savoirs-vivants/station-analyse-qualite-eau/firmware/Docs/latex/driver_f_r_a_m_8c.tex

\doxysection{C:\+/\+\+Users/\+valen/\+\+Documents/\+\+BUT GEII/\+\+SAE601/\+station\+\_\+analyse\+\_\+qualite\+\_\+eau/\+firmware/\+station\+\_\+analyse\+\_\+qualite\+\_\+eau/\+\+Core/\+\+Src/\+driver\+FRAM.c File Reference}
\hypertarget{driver_f_r_a_m_8c}{}\label{driver_f_r_a_m_8c}\index{C:/Users/valen/Documents/BUT GEII/SAE601/station\_analyse\_qualite\_eau/firmware/station\_analyse\_qualite\_eau/Core/Src/driverFRAM.c@{C:/Users/valen/Documents/BUT GEII/SAE601/station\_analyse\_qualite\_eau/firmware/station\_analyse\_qualite\_eau/Core/Src/driverFRAM.c}}
{\ttfamily \+\#include "{}driver\+FRAM.\+h"{}}\newline
{\ttfamily \+\#include $<$string.\+h$>$}\newline
Include dependency graph for driver\+FRAM.\+c:\+
\nopagebreak
\begin{figure}[H]
\begin{center}
\leavevmode
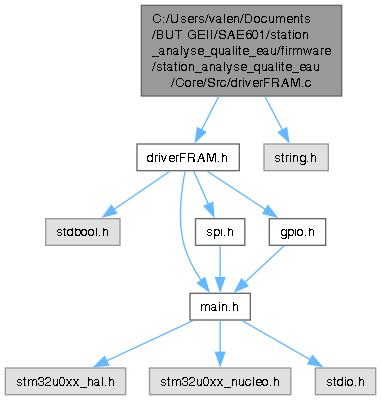
[picture p19: firmware/Docs/html/driver_f_r_a_m_8c__incl.png]

\end{center}
\end{figure}
\doxysubsubsection*{Functions}
\begin{DoxyCompactItemize}
\item 
\doxymbox{\hyperlink{driver_f_r_a_m_8h_a5c79796a1eed5fdbc3537a9758904619}{FRAM\+\_\+\+Result\+\_\+t}} \doxymbox{\hyperlink{driver_f_r_a_m_8c_a05c998c18403bda2555787fbaee7d2c4}{FRAM\+\_\+\+Init}} (\doxymbox{\hyperlink{struct_f_r_a_m__t}{FRAM\+\_\+t}} \texorpdfstring{$\ast$}{*}hfram, SPI\+\_\+\+Handle\+Type\+Def \texorpdfstring{$\ast$}{*}hspi, GPIO\+\_\+\+Type\+Def \texorpdfstring{$\ast$}{*}gpio\+\_\+port, uint16\+\_\+t gpio\+\_\+pin)
\begin{DoxyCompactList}\small\item\em Initialise la structure du driver et sécurise le bus SPI. \end{DoxyCompactList}\item 
\doxymbox{\hyperlink{driver_f_r_a_m_8h_a5c79796a1eed5fdbc3537a9758904619}{FRAM\+\_\+\+Result\+\_\+t}} \doxymbox{\hyperlink{driver_f_r_a_m_8c_a518d592a5f33b7c30320913e25c8d89a}{FRAM\+\_\+\+Write}} (\doxymbox{\hyperlink{struct_f_r_a_m__t}{FRAM\+\_\+t}} \texorpdfstring{$\ast$}{*}hfram, uint32\+\_\+t address, uint8\+\_\+t \texorpdfstring{$\ast$}{*}data, uint16\+\_\+t data\+\_\+size)
\begin{DoxyCompactList}\small\item\em Lance une opération asynchrone d\textquotesingle{}écriture vers la FRAM. \end{DoxyCompactList}\item 
\doxymbox{\hyperlink{driver_f_r_a_m_8h_a5c79796a1eed5fdbc3537a9758904619}{FRAM\+\_\+\+Result\+\_\+t}} \doxymbox{\hyperlink{driver_f_r_a_m_8c_a2ed88753d53d45f89881a459091a064d}{FRAM\+\_\+\+Read}} (\doxymbox{\hyperlink{struct_f_r_a_m__t}{FRAM\+\_\+t}} \texorpdfstring{$\ast$}{*}hfram, uint32\+\_\+t address, uint8\+\_\+t \texorpdfstring{$\ast$}{*}rx\+\_\+data, uint16\+\_\+t data\+\_\+size)
\begin{DoxyCompactList}\small\item\em Lance une opération asynchrone de lecture depuis la FRAM. \end{DoxyCompactList}\item 
\doxymbox{\hyperlink{driver_f_r_a_m_8h_aa90c9f46ed56211e7103e818904525b9}{FRAM\+\_\+\+Status\+\_\+t}} \doxymbox{\hyperlink{driver_f_r_a_m_8c_a352f682afba9d287e205c51423bc79ff}{FRAM\+\_\+\+Get\+Status}} (\doxymbox{\hyperlink{struct_f_r_a_m__t}{FRAM\+\_\+t}} \texorpdfstring{$\ast$}{*}hfram)
\begin{DoxyCompactList}\small\item\em Renvoie le statut opérationnel actuel du driver. \end{DoxyCompactList}\item 
void \doxymbox{\hyperlink{driver_f_r_a_m_8c_a218f6946717b10b3813b1979da4fce49}{FRAM\+\_\+\+Process}} (\doxymbox{\hyperlink{struct_f_r_a_m__t}{FRAM\+\_\+t}} \texorpdfstring{$\ast$}{*}hfram)
\begin{DoxyCompactList}\small\item\em Machine d\textquotesingle{}état du driver. Doit être appelée régulièrement dans la boucle principale. \end{DoxyCompactList}\item 
void \doxymbox{\hyperlink{driver_f_r_a_m_8c_aeafafd463d7b0a53c3f171c5a4949aa9}{FRAM\+\_\+\+Rx\+\_\+\+Callback}} (\doxymbox{\hyperlink{struct_f_r_a_m__t}{FRAM\+\_\+t}} \texorpdfstring{$\ast$}{*}hfram)
\begin{DoxyCompactList}\small\item\em Callback à appeler dans HAL\+\_\+\+SPI\+\_\+\+Rx\+Cplt\+Callback ou HAL\+\_\+\+SPI\+\_\+\+Tx\+Rx\+Cplt\+Callback. \end{DoxyCompactList}\item 
void \doxymbox{\hyperlink{driver_f_r_a_m_8c_a2b2faab018840ee82dca1baa6a25b1d0}{FRAM\+\_\+\+Tx\+\_\+\+Callback}} (\doxymbox{\hyperlink{struct_f_r_a_m__t}{FRAM\+\_\+t}} \texorpdfstring{$\ast$}{*}hfram)
\begin{DoxyCompactList}\small\item\em Callback à appeler dans HAL\+\_\+\+SPI\+\_\+\+Tx\+Cplt\+Callback. \end{DoxyCompactList}\end{DoxyCompactItemize}

\label{driver_f_r_a_m_8c_doc-func-members}
\Hypertarget{driver_f_r_a_m_8c_doc-func-members}
\doxysubsection{Function Documentation}
\Hypertarget{driver_f_r_a_m_8c_a352f682afba9d287e205c51423bc79ff}\index{driverFRAM.c@{driverFRAM.c}!FRAM\_GetStatus@{FRAM\_GetStatus}}
\index{FRAM\_GetStatus@{FRAM\_GetStatus}!driverFRAM.c@{driverFRAM.c}}
\doxysubsubsection{\texorpdfstring{FRAM\_GetStatus()}{FRAM\_GetStatus()}}
{\footnotesize\ttfamily \label{driver_f_r_a_m_8c_a352f682afba9d287e205c51423bc79ff} 
\doxymbox{\hyperlink{driver_f_r_a_m_8h_aa90c9f46ed56211e7103e818904525b9}{FRAM\+\_\+\+Status\+\_\+t}} FRAM\+\_\+\+Get\+Status (\begin{DoxyParamCaption}\item[{\doxymbox{\hyperlink{struct_f_r_a_m__t}{FRAM\+\_\+t}} \texorpdfstring{$\ast$}{*}}]{hfram}{}\end{DoxyParamCaption})}

Renvoie le statut opérationnel actuel du driver. 

\begin{DoxyParams}{Parameters}
{\em hfram} & Pointeur vers l\textquotesingle{}instance du driver FRAM. \\
\hline
\end{DoxyParams}
\begin{DoxyReturn}{Returns}
FRAM\+\_\+\+STATUS\+\_\+\+READY, FRAM\+\_\+\+STATUS\+\_\+\+BUSY, ou FRAM\+\_\+\+STATUS\+\_\+\+ERROR. 
\end{DoxyReturn}
\Hypertarget{driver_f_r_a_m_8c_a05c998c18403bda2555787fbaee7d2c4}\index{driverFRAM.c@{driverFRAM.c}!FRAM\_Init@{FRAM\_Init}}
\index{FRAM\_Init@{FRAM\_Init}!driverFRAM.c@{driverFRAM.c}}
\doxysubsubsection{\texorpdfstring{FRAM\_Init()}{FRAM\_Init()}}
{\footnotesize\ttfamily \label{driver_f_r_a_m_8c_a05c998c18403bda2555787fbaee7d2c4} 
\doxymbox{\hyperlink{driver_f_r_a_m_8h_a5c79796a1eed5fdbc3537a9758904619}{FRAM\+\_\+\+Result\+\_\+t}} FRAM\+\_\+\+Init (\begin{DoxyParamCaption}\item[{\doxymbox{\hyperlink{struct_f_r_a_m__t}{FRAM\+\_\+t}} \texorpdfstring{$\ast$}{*}}]{hfram}{, }\item[{SPI\+\_\+\+Handle\+Type\+Def \texorpdfstring{$\ast$}{*}}]{hspi}{, }\item[{GPIO\+\_\+\+Type\+Def \texorpdfstring{$\ast$}{*}}]{gpio\+\_\+port}{, }\item[{uint16\+\_\+t}]{gpio\+\_\+pin}{}\end{DoxyParamCaption})}

Initialise la structure du driver et sécurise le bus SPI. 

\begin{DoxyParams}{Parameters}
{\em hfram} & Pointeur vers l\textquotesingle{}instance du driver FRAM. \\
\hline
{\em hspi} & Pointeur vers le handle SPI (ex:\+ \&hspi3). \\
\hline
{\em gpio\+\_\+port} & Port GPIO du Chip Select. \\
\hline
{\em gpio\+\_\+pin} & Broche GPIO du Chip Select. \\
\hline
\end{DoxyParams}

\begin{DoxyRetVals}{Return values}
{\em FRAM\+\_\+\+OK} & si succès, sinon un code d\textquotesingle{}erreur synchrone (FRAM\+\_\+\+ERR\+\_\+\+PARAM). \\
\hline
\end{DoxyRetVals}
Here is the caller graph for this function:\+
\nopagebreak
\begin{figure}[H]
\begin{center}
\leavevmode

\end{center}
\end{figure}
\Hypertarget{driver_f_r_a_m_8c_a218f6946717b10b3813b1979da4fce49}\index{driverFRAM.c@{driverFRAM.c}!FRAM\_Process@{FRAM\_Process}}
\index{FRAM\_Process@{FRAM\_Process}!driverFRAM.c@{driverFRAM.c}}
\doxysubsubsection{\texorpdfstring{FRAM\_Process()}{FRAM\_Process()}}
{\footnotesize\ttfamily \label{driver_f_r_a_m_8c_a218f6946717b10b3813b1979da4fce49} 
void FRAM\+\_\+\+Process (\begin{DoxyParamCaption}\item[{\doxymbox{\hyperlink{struct_f_r_a_m__t}{FRAM\+\_\+t}} \texorpdfstring{$\ast$}{*}}]{hfram}{}\end{DoxyParamCaption})}

Machine d\textquotesingle{}état du driver. Doit être appelée régulièrement dans la boucle principale. 

\begin{DoxyParams}{Parameters}
{\em hfram} & Pointeur vers l\textquotesingle{}instance du driver FRAM. \\
\hline
\end{DoxyParams}
Here is the caller graph for this function:\+
\nopagebreak
\begin{figure}[H]
\begin{center}
\leavevmode

\end{center}
\end{figure}
\Hypertarget{driver_f_r_a_m_8c_a2ed88753d53d45f89881a459091a064d}\index{driverFRAM.c@{driverFRAM.c}!FRAM\_Read@{FRAM\_Read}}
\index{FRAM\_Read@{FRAM\_Read}!driverFRAM.c@{driverFRAM.c}}
\doxysubsubsection{\texorpdfstring{FRAM\_Read()}{FRAM\_Read()}}
{\footnotesize\ttfamily \label{driver_f_r_a_m_8c_a2ed88753d53d45f89881a459091a064d} 
\doxymbox{\hyperlink{driver_f_r_a_m_8h_a5c79796a1eed5fdbc3537a9758904619}{FRAM\+\_\+\+Result\+\_\+t}} FRAM\+\_\+\+Read (\begin{DoxyParamCaption}\item[{\doxymbox{\hyperlink{struct_f_r_a_m__t}{FRAM\+\_\+t}} \texorpdfstring{$\ast$}{*}}]{hfram}{, }\item[{uint32\+\_\+t}]{address}{, }\item[{uint8\+\_\+t \texorpdfstring{$\ast$}{*}}]{rx\+\_\+data}{, }\item[{uint16\+\_\+t}]{data\+\_\+size}{}\end{DoxyParamCaption})}

Lance une opération asynchrone de lecture depuis la FRAM. 

\begin{DoxyParams}{Parameters}
{\em hfram} & Pointeur vers l\textquotesingle{}instance du driver FRAM. \\
\hline
{\em address} & Adresse de départ en mémoire (doit être \texorpdfstring{$<$}{<} FRAM\+\_\+\+MAX\+\_\+\+ADDRESS). \\
\hline
{\em rx\+\_\+data} & Pointeur vers le buffer où stocker les données lues. \\
\hline
{\em data\+\_\+size} & Nombre d\textquotesingle{}octets à lire. \\
\hline
\end{DoxyParams}

\begin{DoxyRetVals}{Return values}
{\em FRAM\+\_\+\+OK} & si l\textquotesingle{}opération est acceptée, sinon un code d\textquotesingle{}erreur (BUSY, PARAM). \\
\hline
\end{DoxyRetVals}
Here is the caller graph for this function:\+
\nopagebreak
\begin{figure}[H]
\begin{center}
\leavevmode

\end{center}
\end{figure}
\Hypertarget{driver_f_r_a_m_8c_aeafafd463d7b0a53c3f171c5a4949aa9}\index{driverFRAM.c@{driverFRAM.c}!FRAM\_Rx\_Callback@{FRAM\_Rx\_Callback}}
\index{FRAM\_Rx\_Callback@{FRAM\_Rx\_Callback}!driverFRAM.c@{driverFRAM.c}}
\doxysubsubsection{\texorpdfstring{FRAM\_Rx\_Callback()}{FRAM\_Rx\_Callback()}}
{\footnotesize\ttfamily \label{driver_f_r_a_m_8c_aeafafd463d7b0a53c3f171c5a4949aa9} 
void FRAM\+\_\+\+Rx\+\_\+\+Callback (\begin{DoxyParamCaption}\item[{\doxymbox{\hyperlink{struct_f_r_a_m__t}{FRAM\+\_\+t}} \texorpdfstring{$\ast$}{*}}]{hfram}{}\end{DoxyParamCaption})}

Callback à appeler dans HAL\+\_\+\+SPI\+\_\+\+Rx\+Cplt\+Callback ou HAL\+\_\+\+SPI\+\_\+\+Tx\+Rx\+Cplt\+Callback. 

\begin{DoxyParams}{Parameters}
{\em hfram} & Pointeur vers l\textquotesingle{}instance du driver FRAM. \\
\hline
\end{DoxyParams}
Here is the caller graph for this function:\+
\nopagebreak
\begin{figure}[H]
\begin{center}
\leavevmode

\end{center}
\end{figure}
\Hypertarget{driver_f_r_a_m_8c_a2b2faab018840ee82dca1baa6a25b1d0}\index{driverFRAM.c@{driverFRAM.c}!FRAM\_Tx\_Callback@{FRAM\_Tx\_Callback}}
\index{FRAM\_Tx\_Callback@{FRAM\_Tx\_Callback}!driverFRAM.c@{driverFRAM.c}}
\doxysubsubsection{\texorpdfstring{FRAM\_Tx\_Callback()}{FRAM\_Tx\_Callback()}}
{\footnotesize\ttfamily \label{driver_f_r_a_m_8c_a2b2faab018840ee82dca1baa6a25b1d0} 
void FRAM\+\_\+\+Tx\+\_\+\+Callback (\begin{DoxyParamCaption}\item[{\doxymbox{\hyperlink{struct_f_r_a_m__t}{FRAM\+\_\+t}} \texorpdfstring{$\ast$}{*}}]{hfram}{}\end{DoxyParamCaption})}

Callback à appeler dans HAL\+\_\+\+SPI\+\_\+\+Tx\+Cplt\+Callback. 

\begin{DoxyParams}{Parameters}
{\em hfram} & Pointeur vers l\textquotesingle{}instance du driver FRAM. \\
\hline
\end{DoxyParams}
Here is the caller graph for this function:\+
\nopagebreak
\begin{figure}[H]
\begin{center}
\leavevmode

\end{center}
\end{figure}
\Hypertarget{driver_f_r_a_m_8c_a518d592a5f33b7c30320913e25c8d89a}\index{driverFRAM.c@{driverFRAM.c}!FRAM\_Write@{FRAM\_Write}}
\index{FRAM\_Write@{FRAM\_Write}!driverFRAM.c@{driverFRAM.c}}
\doxysubsubsection{\texorpdfstring{FRAM\_Write()}{FRAM\_Write()}}
{\footnotesize\ttfamily \label{driver_f_r_a_m_8c_a518d592a5f33b7c30320913e25c8d89a} 
\doxymbox{\hyperlink{driver_f_r_a_m_8h_a5c79796a1eed5fdbc3537a9758904619}{FRAM\+\_\+\+Result\+\_\+t}} FRAM\+\_\+\+Write (\begin{DoxyParamCaption}\item[{\doxymbox{\hyperlink{struct_f_r_a_m__t}{FRAM\+\_\+t}} \texorpdfstring{$\ast$}{*}}]{hfram}{, }\item[{uint32\+\_\+t}]{address}{, }\item[{uint8\+\_\+t \texorpdfstring{$\ast$}{*}}]{data}{, }\item[{uint16\+\_\+t}]{data\+\_\+size}{}\end{DoxyParamCaption})}

Lance une opération asynchrone d\textquotesingle{}écriture vers la FRAM. 

\begin{DoxyParams}{Parameters}
{\em hfram} & Pointeur vers l\textquotesingle{}instance du driver FRAM. \\
\hline
{\em address} & Adresse de départ en mémoire (doit être \texorpdfstring{$<$}{<} FRAM\+\_\+\+MAX\+\_\+\+ADDRESS). \\
\hline
{\em data} & Pointeur vers les données à écrire. \\
\hline
{\em data\+\_\+size} & Nombre d\textquotesingle{}octets à écrire. \\
\hline
\end{DoxyParams}

\begin{DoxyRetVals}{Return values}
{\em FRAM\+\_\+\+OK} & si l\textquotesingle{}opération est acceptée, sinon un code d\textquotesingle{}erreur (BUSY, PARAM). \\
\hline
\end{DoxyRetVals}
Here is the caller graph for this function:\+
\nopagebreak
\begin{figure}[H]
\begin{center}
\leavevmode

\end{center}
\end{figure}
