savoirs-vivants/station-analyse-qualite-eau/firmware/Docs/latex/driver_lo_ra_app_8c.tex

\doxysection{C:\+/\+\+Users/\+valen/\+\+Documents/\+\+BUT GEII/\+\+SAE601/\+station\+\_\+analyse\+\_\+qualite\+\_\+eau/\+firmware/\+station\+\_\+analyse\+\_\+qualite\+\_\+eau/\+\+Core/\+\+Src/\+driver\+Lo\+Ra\+App.c File Reference}
\hypertarget{driver_lo_ra_app_8c}{}\label{driver_lo_ra_app_8c}\index{C:/Users/valen/Documents/BUT GEII/SAE601/station\_analyse\_qualite\_eau/firmware/station\_analyse\_qualite\_eau/Core/Src/driverLoRaApp.c@{C:/Users/valen/Documents/BUT GEII/SAE601/station\_analyse\_qualite\_eau/firmware/station\_analyse\_qualite\_eau/Core/Src/driverLoRaApp.c}}
{\ttfamily \+\#include "{}driver\+Lo\+Ra\+App.\+h"{}}\newline
Include dependency graph for driver\+Lo\+Ra\+App.\+c:\+
\nopagebreak
\begin{figure}[H]
\begin{center}
\leavevmode
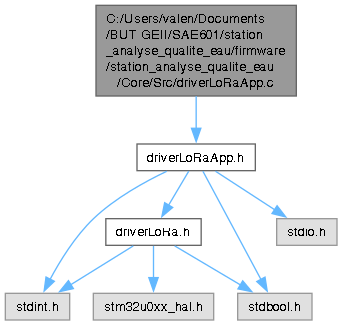
[picture p28: firmware/Docs/html/driver_lo_ra_app_8c__incl.png]

\end{center}
\end{figure}
\doxysubsubsection*{Functions}
\begin{DoxyCompactItemize}
\item 
void \doxymbox{\hyperlink{driver_lo_ra_app_8c_a42db2c6d3925f1c86ebfdd004cc7da83}{Lo\+Ra\+\_\+\+App\+\_\+\+Init}} (\doxymbox{\hyperlink{struct_lo_ra_w_a_n___manager__t}{Lo\+Ra\+WAN\+\_\+\+Manager\+\_\+t}} \texorpdfstring{$\ast$}{*}hlorapp, \doxymbox{\hyperlink{struct_lo_ra__t}{Lo\+Ra\+\_\+t}} \texorpdfstring{$\ast$}{*}hlora, const \doxymbox{\hyperlink{struct_lo_ra___command__t}{Lo\+Ra\+\_\+\+Command\+\_\+t}} \texorpdfstring{$\ast$}{*}cmds)
\item 
void \doxymbox{\hyperlink{driver_lo_ra_app_8c_a6f48cdb117beed1327cee06821cd0800}{Lo\+Ra\+\_\+\+App\+\_\+\+Process}} (\doxymbox{\hyperlink{struct_lo_ra_w_a_n___manager__t}{Lo\+Ra\+WAN\+\_\+\+Manager\+\_\+t}} \texorpdfstring{$\ast$}{*}hlorapp)
\end{DoxyCompactItemize}

\label{driver_lo_ra_app_8c_doc-func-members}
\Hypertarget{driver_lo_ra_app_8c_doc-func-members}
\doxysubsection{Function Documentation}
\Hypertarget{driver_lo_ra_app_8c_a42db2c6d3925f1c86ebfdd004cc7da83}\index{driverLoRaApp.c@{driverLoRaApp.c}!LoRa\_App\_Init@{LoRa\_App\_Init}}
\index{LoRa\_App\_Init@{LoRa\_App\_Init}!driverLoRaApp.c@{driverLoRaApp.c}}
\doxysubsubsection{\texorpdfstring{LoRa\_App\_Init()}{LoRa\_App\_Init()}}
{\footnotesize\ttfamily \label{driver_lo_ra_app_8c_a42db2c6d3925f1c86ebfdd004cc7da83} 
void Lo\+Ra\+\_\+\+App\+\_\+\+Init (\begin{DoxyParamCaption}\item[{\doxymbox{\hyperlink{struct_lo_ra_w_a_n___manager__t}{Lo\+Ra\+WAN\+\_\+\+Manager\+\_\+t}} \texorpdfstring{$\ast$}{*}}]{hlorapp}{, }\item[{\doxymbox{\hyperlink{struct_lo_ra__t}{Lo\+Ra\+\_\+t}} \texorpdfstring{$\ast$}{*}}]{hlora}{, }\item[{const \doxymbox{\hyperlink{struct_lo_ra___command__t}{Lo\+Ra\+\_\+\+Command\+\_\+t}} \texorpdfstring{$\ast$}{*}}]{cmds}{}\end{DoxyParamCaption})}

\Hypertarget{driver_lo_ra_app_8c_a6f48cdb117beed1327cee06821cd0800}\index{driverLoRaApp.c@{driverLoRaApp.c}!LoRa\_App\_Process@{LoRa\_App\_Process}}
\index{LoRa\_App\_Process@{LoRa\_App\_Process}!driverLoRaApp.c@{driverLoRaApp.c}}
\doxysubsubsection{\texorpdfstring{LoRa\_App\_Process()}{LoRa\_App\_Process()}}
{\footnotesize\ttfamily \label{driver_lo_ra_app_8c_a6f48cdb117beed1327cee06821cd0800} 
void Lo\+Ra\+\_\+\+App\+\_\+\+Process (\begin{DoxyParamCaption}\item[{\doxymbox{\hyperlink{struct_lo_ra_w_a_n___manager__t}{Lo\+Ra\+WAN\+\_\+\+Manager\+\_\+t}} \texorpdfstring{$\ast$}{*}}]{hlorapp}{}\end{DoxyParamCaption})}

Here is the call graph for this function:\+
\nopagebreak
\begin{figure}[H]
\begin{center}
\leavevmode

\end{center}
\end{figure}
