savoirs-vivants/station-analyse-qualite-eau/firmware/Docs/latex/driver_lo_ra_app_8h.tex

\doxysection{C:\+/\+\+Users/\+valen/\+\+Documents/\+\+BUT GEII/\+\+SAE601/\+station\+\_\+analyse\+\_\+qualite\+\_\+eau/\+firmware/\+station\+\_\+analyse\+\_\+qualite\+\_\+eau/\+\+Core/\+\+Inc/\+driver\+Lo\+Ra\+App.h File Reference}
\hypertarget{driver_lo_ra_app_8h}{}\label{driver_lo_ra_app_8h}\index{C:/Users/valen/Documents/BUT GEII/SAE601/station\_analyse\_qualite\_eau/firmware/station\_analyse\_qualite\_eau/Core/Inc/driverLoRaApp.h@{C:/Users/valen/Documents/BUT GEII/SAE601/station\_analyse\_qualite\_eau/firmware/station\_analyse\_qualite\_eau/Core/Inc/driverLoRaApp.h}}
{\ttfamily \+\#include $<$stdint.\+h$>$}\newline
{\ttfamily \+\#include $<$stdbool.\+h$>$}\newline
{\ttfamily \+\#include $<$stdio.\+h$>$}\newline
{\ttfamily \+\#include "{}driver\+Lo\+Ra.\+h"{}}\newline
Include dependency graph for driver\+Lo\+Ra\+App.\+h:\+
\nopagebreak
\begin{figure}[H]
\begin{center}
\leavevmode
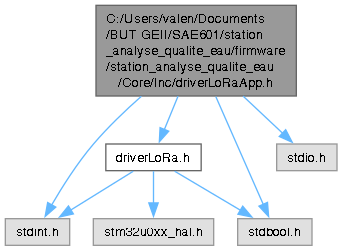
[picture p29: firmware/Docs/html/driver_lo_ra_app_8h__incl.png]

\end{center}
\end{figure}
This graph shows which files directly or indirectly include this file:\+
\nopagebreak
\begin{figure}[H]
\begin{center}
\leavevmode
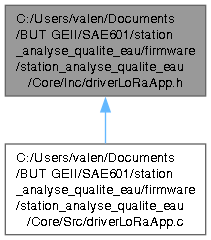
[picture p30: firmware/Docs/html/driver_lo_ra_app_8h__dep__incl.png]

\end{center}
\end{figure}
\doxysubsubsection*{Data Structures}
\begin{DoxyCompactItemize}
\item 
struct \doxymbox{\hyperlink{struct_lo_ra___command__t}{Lo\+Ra\+\_\+\+Command\+\_\+t}}
\item 
struct \doxymbox{\hyperlink{struct_lo_ra_w_a_n___manager__t}{Lo\+Ra\+WAN\+\_\+\+Manager\+\_\+t}}
\end{DoxyCompactItemize}
\doxysubsubsection*{Functions}
\begin{DoxyCompactItemize}
\item 
void \doxymbox{\hyperlink{driver_lo_ra_app_8h_a42db2c6d3925f1c86ebfdd004cc7da83}{Lo\+Ra\+\_\+\+App\+\_\+\+Init}} (\doxymbox{\hyperlink{struct_lo_ra_w_a_n___manager__t}{Lo\+Ra\+WAN\+\_\+\+Manager\+\_\+t}} \texorpdfstring{$\ast$}{*}hlorapp, \doxymbox{\hyperlink{struct_lo_ra__t}{Lo\+Ra\+\_\+t}} \texorpdfstring{$\ast$}{*}hlora, const \doxymbox{\hyperlink{struct_lo_ra___command__t}{Lo\+Ra\+\_\+\+Command\+\_\+t}} \texorpdfstring{$\ast$}{*}cmds)
\item 
void \doxymbox{\hyperlink{driver_lo_ra_app_8h_a6f48cdb117beed1327cee06821cd0800}{Lo\+Ra\+\_\+\+App\+\_\+\+Process}} (\doxymbox{\hyperlink{struct_lo_ra_w_a_n___manager__t}{Lo\+Ra\+WAN\+\_\+\+Manager\+\_\+t}} \texorpdfstring{$\ast$}{*}hlorapp)
\end{DoxyCompactItemize}

\label{driver_lo_ra_app_8h_doc-func-members}
\Hypertarget{driver_lo_ra_app_8h_doc-func-members}
\doxysubsection{Function Documentation}
\Hypertarget{driver_lo_ra_app_8h_a42db2c6d3925f1c86ebfdd004cc7da83}\index{driverLoRaApp.h@{driverLoRaApp.h}!LoRa\_App\_Init@{LoRa\_App\_Init}}
\index{LoRa\_App\_Init@{LoRa\_App\_Init}!driverLoRaApp.h@{driverLoRaApp.h}}
\doxysubsubsection{\texorpdfstring{LoRa\_App\_Init()}{LoRa\_App\_Init()}}
{\footnotesize\ttfamily \label{driver_lo_ra_app_8h_a42db2c6d3925f1c86ebfdd004cc7da83} 
void Lo\+Ra\+\_\+\+App\+\_\+\+Init (\begin{DoxyParamCaption}\item[{\doxymbox{\hyperlink{struct_lo_ra_w_a_n___manager__t}{Lo\+Ra\+WAN\+\_\+\+Manager\+\_\+t}} \texorpdfstring{$\ast$}{*}}]{hlorapp}{, }\item[{\doxymbox{\hyperlink{struct_lo_ra__t}{Lo\+Ra\+\_\+t}} \texorpdfstring{$\ast$}{*}}]{hlora}{, }\item[{const \doxymbox{\hyperlink{struct_lo_ra___command__t}{Lo\+Ra\+\_\+\+Command\+\_\+t}} \texorpdfstring{$\ast$}{*}}]{cmds}{}\end{DoxyParamCaption})}

\Hypertarget{driver_lo_ra_app_8h_a6f48cdb117beed1327cee06821cd0800}\index{driverLoRaApp.h@{driverLoRaApp.h}!LoRa\_App\_Process@{LoRa\_App\_Process}}
\index{LoRa\_App\_Process@{LoRa\_App\_Process}!driverLoRaApp.h@{driverLoRaApp.h}}
\doxysubsubsection{\texorpdfstring{LoRa\_App\_Process()}{LoRa\_App\_Process()}}
{\footnotesize\ttfamily \label{driver_lo_ra_app_8h_a6f48cdb117beed1327cee06821cd0800} 
void Lo\+Ra\+\_\+\+App\+\_\+\+Process (\begin{DoxyParamCaption}\item[{\doxymbox{\hyperlink{struct_lo_ra_w_a_n___manager__t}{Lo\+Ra\+WAN\+\_\+\+Manager\+\_\+t}} \texorpdfstring{$\ast$}{*}}]{hlorapp}{}\end{DoxyParamCaption})}

Here is the call graph for this function:\+
\nopagebreak
\begin{figure}[H]
\begin{center}
\leavevmode

\end{center}
\end{figure}
