savoirs-vivants/station-analyse-qualite-eau/firmware/Docs/latex/driver_r_t_c_8c.tex

\doxysection{C:\+/\+\+Users/\+valen/\+\+Documents/\+\+BUT GEII/\+\+SAE601/\+station\+\_\+analyse\+\_\+qualite\+\_\+eau/\+firmware/\+station\+\_\+analyse\+\_\+qualite\+\_\+eau/\+\+Core/\+\+Src/\+driver\+RTC.c File Reference}
\hypertarget{driver_r_t_c_8c}{}\label{driver_r_t_c_8c}\index{C:/Users/valen/Documents/BUT GEII/SAE601/station\_analyse\_qualite\_eau/firmware/station\_analyse\_qualite\_eau/Core/Src/driverRTC.c@{C:/Users/valen/Documents/BUT GEII/SAE601/station\_analyse\_qualite\_eau/firmware/station\_analyse\_qualite\_eau/Core/Src/driverRTC.c}}
{\ttfamily \+\#include "{}driver\+RTC.\+h"{}}\newline
Include dependency graph for driver\+RTC.\+c:\+
\nopagebreak
\begin{figure}[H]
\begin{center}
\leavevmode
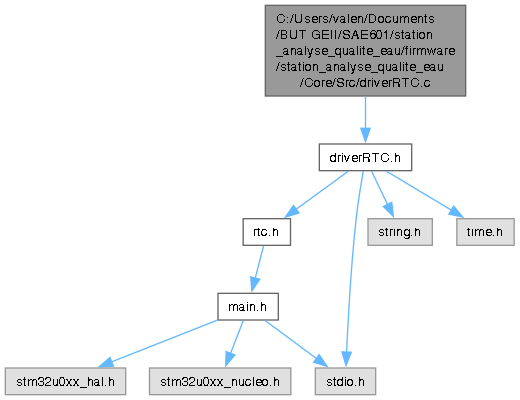
[picture p34: firmware/Docs/html/driver_r_t_c_8c__incl.png]

\end{center}
\end{figure}
\doxysubsubsection*{Functions}
\begin{DoxyCompactItemize}
\item 
void \doxymbox{\hyperlink{driver_r_t_c_8c_a494a13f6dc06fc1b330d8ac7f15f1c67}{config\+RTC}} (RTC\+\_\+\+Handle\+Type\+Def \texorpdfstring{$\ast$}{*}hrtc, RTC\+\_\+\+Time\+Type\+Def \texorpdfstring{$\ast$}{*}s\+Time, RTC\+\_\+\+Date\+Type\+Def \texorpdfstring{$\ast$}{*}s\+Date)
\item 
uint32\+\_\+t \doxymbox{\hyperlink{driver_r_t_c_8c_adaa0993b12bc61940e096e6a8d791dcd}{Get\+\_\+\+UNIX\+\_\+\+Timestamp}} (RTC\+\_\+\+Time\+Type\+Def \texorpdfstring{$\ast$}{*}s\+Time\+\_\+read, RTC\+\_\+\+Date\+Type\+Def \texorpdfstring{$\ast$}{*}s\+Date\+\_\+read)
\end{DoxyCompactItemize}

\label{driver_r_t_c_8c_doc-func-members}
\Hypertarget{driver_r_t_c_8c_doc-func-members}
\doxysubsection{Function Documentation}
\Hypertarget{driver_r_t_c_8c_a494a13f6dc06fc1b330d8ac7f15f1c67}\index{driverRTC.c@{driverRTC.c}!configRTC@{configRTC}}
\index{configRTC@{configRTC}!driverRTC.c@{driverRTC.c}}
\doxysubsubsection{\texorpdfstring{configRTC()}{configRTC()}}
{\footnotesize\ttfamily \label{driver_r_t_c_8c_a494a13f6dc06fc1b330d8ac7f15f1c67} 
void config\+RTC (\begin{DoxyParamCaption}\item[{RTC\+\_\+\+Handle\+Type\+Def \texorpdfstring{$\ast$}{*}}]{hrtc}{, }\item[{RTC\+\_\+\+Time\+Type\+Def \texorpdfstring{$\ast$}{*}}]{s\+Time}{, }\item[{RTC\+\_\+\+Date\+Type\+Def \texorpdfstring{$\ast$}{*}}]{s\+Date}{}\end{DoxyParamCaption})}

Here is the call graph for this function:\+
\nopagebreak
\begin{figure}[H]
\begin{center}
\leavevmode

\end{center}
\end{figure}
Here is the caller graph for this function:\+
\nopagebreak
\begin{figure}[H]
\begin{center}
\leavevmode

\end{center}
\end{figure}
\Hypertarget{driver_r_t_c_8c_adaa0993b12bc61940e096e6a8d791dcd}\index{driverRTC.c@{driverRTC.c}!Get\_UNIX\_Timestamp@{Get\_UNIX\_Timestamp}}
\index{Get\_UNIX\_Timestamp@{Get\_UNIX\_Timestamp}!driverRTC.c@{driverRTC.c}}
\doxysubsubsection{\texorpdfstring{Get\_UNIX\_Timestamp()}{Get\_UNIX\_Timestamp()}}
{\footnotesize\ttfamily \label{driver_r_t_c_8c_adaa0993b12bc61940e096e6a8d791dcd} 
uint32\+\_\+t Get\+\_\+\+UNIX\+\_\+\+Timestamp (\begin{DoxyParamCaption}\item[{RTC\+\_\+\+Time\+Type\+Def \texorpdfstring{$\ast$}{*}}]{s\+Time\+\_\+read}{, }\item[{RTC\+\_\+\+Date\+Type\+Def \texorpdfstring{$\ast$}{*}}]{s\+Date\+\_\+read}{}\end{DoxyParamCaption})}

Here is the caller graph for this function:\+
\nopagebreak
\begin{figure}[H]
\begin{center}
\leavevmode

\end{center}
\end{figure}
