savoirs-vivants/station-analyse-qualite-eau/firmware/Docs/latex/driver_r_t_c_8h.tex

\doxysection{C:\+/\+\+Users/\+valen/\+\+Documents/\+\+BUT GEII/\+\+SAE601/\+station\+\_\+analyse\+\_\+qualite\+\_\+eau/\+firmware/\+station\+\_\+analyse\+\_\+qualite\+\_\+eau/\+\+Core/\+\+Inc/\+driver\+RTC.h File Reference}
\hypertarget{driver_r_t_c_8h}{}\label{driver_r_t_c_8h}\index{C:/Users/valen/Documents/BUT GEII/SAE601/station\_analyse\_qualite\_eau/firmware/station\_analyse\_qualite\_eau/Core/Inc/driverRTC.h@{C:/Users/valen/Documents/BUT GEII/SAE601/station\_analyse\_qualite\_eau/firmware/station\_analyse\_qualite\_eau/Core/Inc/driverRTC.h}}
{\ttfamily \+\#include "{}rtc.\+h"{}}\newline
{\ttfamily \+\#include $<$stdio.\+h$>$}\newline
{\ttfamily \+\#include $<$string.\+h$>$}\newline
{\ttfamily \+\#include $<$time.\+h$>$}\newline
Include dependency graph for driver\+RTC.\+h:\+
\nopagebreak
\begin{figure}[H]
\begin{center}
\leavevmode
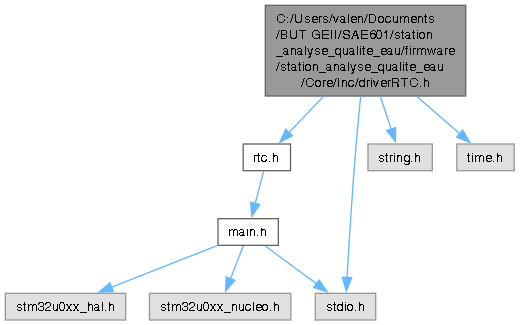
[picture p35: firmware/Docs/html/driver_r_t_c_8h__incl.png]

\end{center}
\end{figure}
This graph shows which files directly or indirectly include this file:\+
\nopagebreak
\begin{figure}[H]
\begin{center}
\leavevmode
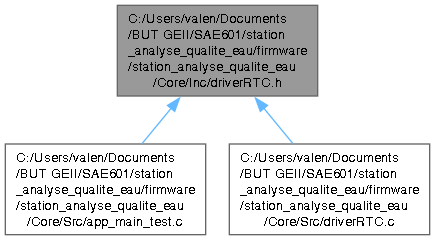
[picture p36: firmware/Docs/html/driver_r_t_c_8h__dep__incl.png]

\end{center}
\end{figure}
\doxysubsubsection*{Macros}
\begin{DoxyCompactItemize}
\item 
\+\#define \doxymbox{\hyperlink{driver_r_t_c_8h_a5f40ba753c005602f9084eeeb5cffd11}{IS\+\_\+\+SUMMER\+\_\+\+TIME}}~1
\end{DoxyCompactItemize}
\doxysubsubsection*{Functions}
\begin{DoxyCompactItemize}
\item 
void \doxymbox{\hyperlink{driver_r_t_c_8h_a494a13f6dc06fc1b330d8ac7f15f1c67}{config\+RTC}} (RTC\+\_\+\+Handle\+Type\+Def \texorpdfstring{$\ast$}{*}hrtc, RTC\+\_\+\+Time\+Type\+Def \texorpdfstring{$\ast$}{*}s\+Time, RTC\+\_\+\+Date\+Type\+Def \texorpdfstring{$\ast$}{*}s\+Date)
\item 
uint32\+\_\+t \doxymbox{\hyperlink{driver_r_t_c_8h_adaa0993b12bc61940e096e6a8d791dcd}{Get\+\_\+\+UNIX\+\_\+\+Timestamp}} (RTC\+\_\+\+Time\+Type\+Def \texorpdfstring{$\ast$}{*}s\+Time\+\_\+read, RTC\+\_\+\+Date\+Type\+Def \texorpdfstring{$\ast$}{*}s\+Date\+\_\+read)
\end{DoxyCompactItemize}

\label{driver_r_t_c_8h_doc-define-members}
\Hypertarget{driver_r_t_c_8h_doc-define-members}
\doxysubsection{Macro Definition Documentation}
\Hypertarget{driver_r_t_c_8h_a5f40ba753c005602f9084eeeb5cffd11}\index{driverRTC.h@{driverRTC.h}!IS\_SUMMER\_TIME@{IS\_SUMMER\_TIME}}
\index{IS\_SUMMER\_TIME@{IS\_SUMMER\_TIME}!driverRTC.h@{driverRTC.h}}
\doxysubsubsection{\texorpdfstring{IS\_SUMMER\_TIME}{IS\_SUMMER\_TIME}}
{\footnotesize\ttfamily \label{driver_r_t_c_8h_a5f40ba753c005602f9084eeeb5cffd11} 
\+\#define IS\+\_\+\+SUMMER\+\_\+\+TIME~1}

\label{driver_r_t_c_8h_doc-func-members}
\Hypertarget{driver_r_t_c_8h_doc-func-members}
\doxysubsection{Function Documentation}
\Hypertarget{driver_r_t_c_8h_a494a13f6dc06fc1b330d8ac7f15f1c67}\index{driverRTC.h@{driverRTC.h}!configRTC@{configRTC}}
\index{configRTC@{configRTC}!driverRTC.h@{driverRTC.h}}
\doxysubsubsection{\texorpdfstring{configRTC()}{configRTC()}}
{\footnotesize\ttfamily \label{driver_r_t_c_8h_a494a13f6dc06fc1b330d8ac7f15f1c67} 
void config\+RTC (\begin{DoxyParamCaption}\item[{RTC\+\_\+\+Handle\+Type\+Def \texorpdfstring{$\ast$}{*}}]{hrtc}{, }\item[{RTC\+\_\+\+Time\+Type\+Def \texorpdfstring{$\ast$}{*}}]{s\+Time}{, }\item[{RTC\+\_\+\+Date\+Type\+Def \texorpdfstring{$\ast$}{*}}]{s\+Date}{}\end{DoxyParamCaption})}

Here is the call graph for this function:\+
\nopagebreak
\begin{figure}[H]
\begin{center}
\leavevmode

\end{center}
\end{figure}
Here is the caller graph for this function:\+
\nopagebreak
\begin{figure}[H]
\begin{center}
\leavevmode

\end{center}
\end{figure}
\Hypertarget{driver_r_t_c_8h_adaa0993b12bc61940e096e6a8d791dcd}\index{driverRTC.h@{driverRTC.h}!Get\_UNIX\_Timestamp@{Get\_UNIX\_Timestamp}}
\index{Get\_UNIX\_Timestamp@{Get\_UNIX\_Timestamp}!driverRTC.h@{driverRTC.h}}
\doxysubsubsection{\texorpdfstring{Get\_UNIX\_Timestamp()}{Get\_UNIX\_Timestamp()}}
{\footnotesize\ttfamily \label{driver_r_t_c_8h_adaa0993b12bc61940e096e6a8d791dcd} 
uint32\+\_\+t Get\+\_\+\+UNIX\+\_\+\+Timestamp (\begin{DoxyParamCaption}\item[{RTC\+\_\+\+Time\+Type\+Def \texorpdfstring{$\ast$}{*}}]{s\+Time\+\_\+read}{, }\item[{RTC\+\_\+\+Date\+Type\+Def \texorpdfstring{$\ast$}{*}}]{s\+Date\+\_\+read}{}\end{DoxyParamCaption})}

Here is the caller graph for this function:\+
\nopagebreak
\begin{figure}[H]
\begin{center}
\leavevmode

\end{center}
\end{figure}
