savoirs-vivants/station-analyse-qualite-eau/firmware/Docs/latex/spi_8h.tex

\doxysection{C:\+/\+\+Users/\+valen/\+\+Documents/\+\+BUT GEII/\+\+SAE601/\+station\+\_\+analyse\+\_\+qualite\+\_\+eau/\+firmware/\+station\+\_\+analyse\+\_\+qualite\+\_\+eau/\+\+Core/\+\+Inc/\+spi.h File Reference}
\hypertarget{spi_8h}{}\label{spi_8h}\index{C:/Users/valen/Documents/BUT GEII/SAE601/station\_analyse\_qualite\_eau/firmware/station\_analyse\_qualite\_eau/Core/Inc/spi.h@{C:/Users/valen/Documents/BUT GEII/SAE601/station\_analyse\_qualite\_eau/firmware/station\_analyse\_qualite\_eau/Core/Inc/spi.h}}

This file contains all the function prototypes for the \doxylink{spi_8c}{spi.\+c} file.  

{\ttfamily \+\#include "{}main.\+h"{}}\newline
Include dependency graph for spi.\+h:\+
\nopagebreak
\begin{figure}[H]
\begin{center}
\leavevmode
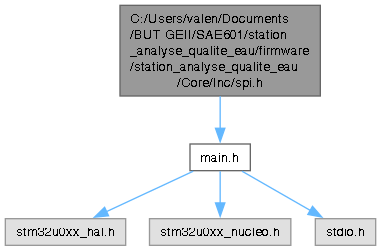
[picture p41: firmware/Docs/html/spi_8h__incl.png]

\end{center}
\end{figure}
This graph shows which files directly or indirectly include this file:\+
\nopagebreak
\begin{figure}[H]
\begin{center}
\leavevmode
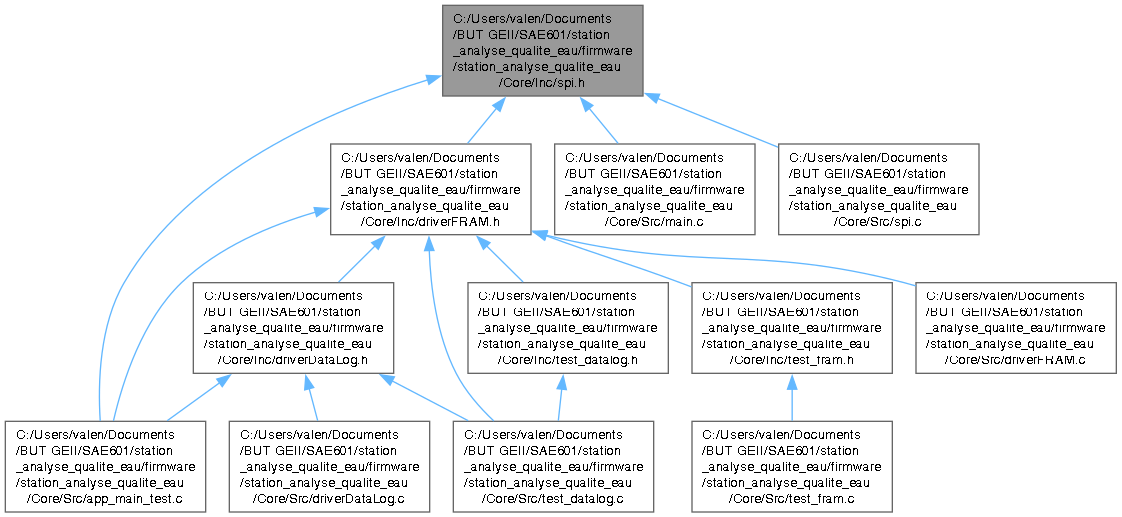
[picture p42: firmware/Docs/html/spi_8h__dep__incl.png]

\end{center}
\end{figure}
\doxysubsubsection*{Functions}
\begin{DoxyCompactItemize}
\item 
void \doxymbox{\hyperlink{spi_8h_a03aff927b2793cac09e443299c6d6e7e}{MX\+\_\+\+SPI3\+\_\+\+Init}} (void)
\end{DoxyCompactItemize}
\doxysubsubsection*{Variables}
\begin{DoxyCompactItemize}
\item 
SPI\+\_\+\+Handle\+Type\+Def \doxymbox{\hyperlink{spi_8h_aec51920045aad7f70cbfd1f58228d866}{hspi3}}
\end{DoxyCompactItemize}

\doxysubsection{Detailed Description}
This file contains all the function prototypes for the \doxylink{spi_8c}{spi.\+c} file. 

\begin{DoxyAttention}{Attention}

\end{DoxyAttention}
Copyright (c) 2026 STMicroelectronics. All rights reserved.

This software is licensed under terms that can be found in the LICENSE file in the root directory of this software component. If no LICENSE file comes with this software, it is provided AS-\/\+IS. 

\label{spi_8h_doc-func-members}
\Hypertarget{spi_8h_doc-func-members}
\doxysubsection{Function Documentation}
\Hypertarget{spi_8h_a03aff927b2793cac09e443299c6d6e7e}\index{spi.h@{spi.h}!MX\_SPI3\_Init@{MX\_SPI3\_Init}}
\index{MX\_SPI3\_Init@{MX\_SPI3\_Init}!spi.h@{spi.h}}
\doxysubsubsection{\texorpdfstring{MX\_SPI3\_Init()}{MX\_SPI3\_Init()}}
{\footnotesize\ttfamily \label{spi_8h_a03aff927b2793cac09e443299c6d6e7e} 
void MX\+\_\+\+SPI3\+\_\+\+Init (\begin{DoxyParamCaption}\item[{void}]{}{}\end{DoxyParamCaption})}

Here is the call graph for this function:\+
\nopagebreak
\begin{figure}[H]
\begin{center}
\leavevmode

\end{center}
\end{figure}
Here is the caller graph for this function:\+
\nopagebreak
\begin{figure}[H]
\begin{center}
\leavevmode

\end{center}
\end{figure}

\label{spi_8h_doc-var-members}
\Hypertarget{spi_8h_doc-var-members}
\doxysubsection{Variable Documentation}
\Hypertarget{spi_8h_aec51920045aad7f70cbfd1f58228d866}\index{spi.h@{spi.h}!hspi3@{hspi3}}
\index{hspi3@{hspi3}!spi.h@{spi.h}}
\doxysubsubsection{\texorpdfstring{hspi3}{hspi3}}
{\footnotesize\ttfamily \label{spi_8h_aec51920045aad7f70cbfd1f58228d866} 
SPI\+\_\+\+Handle\+Type\+Def hspi3\hspace{0.3cm}{\ttfamily [extern]}}
