savoirs-vivants/station-analyse-qualite-eau/firmware/Docs/latex/stm32u0xx__hal__msp_8c.tex

\doxysection{C:\+/\+\+Users/\+valen/\+\+Documents/\+\+BUT GEII/\+\+SAE601/\+station\+\_\+analyse\+\_\+qualite\+\_\+eau/\+firmware/\+station\+\_\+analyse\+\_\+qualite\+\_\+eau/\+\+Core/\+\+Src/\+stm32u0xx\+\_\+hal\+\_\+msp.c File Reference}
\hypertarget{stm32u0xx__hal__msp_8c}{}\label{stm32u0xx__hal__msp_8c}\index{C:/Users/valen/Documents/BUT GEII/SAE601/station\_analyse\_qualite\_eau/firmware/station\_analyse\_qualite\_eau/Core/Src/stm32u0xx\_hal\_msp.c@{C:/Users/valen/Documents/BUT GEII/SAE601/station\_analyse\_qualite\_eau/firmware/station\_analyse\_qualite\_eau/Core/Src/stm32u0xx\_hal\_msp.c}}

This file provides code for the MSP Initialization and de-\/\+Initialization codes.  

{\ttfamily \+\#include "{}main.\+h"{}}\newline
Include dependency graph for stm32u0xx\+\_\+hal\+\_\+msp.\+c:\+
\nopagebreak
\begin{figure}[H]
\begin{center}
\leavevmode
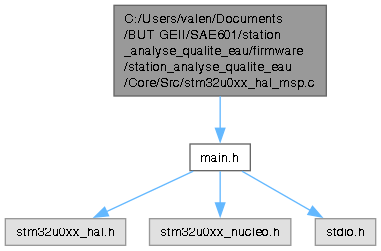
[picture p43: firmware/Docs/html/stm32u0xx__hal__msp_8c__incl.png]

\end{center}
\end{figure}
\doxysubsubsection*{Functions}
\begin{DoxyCompactItemize}
\item 
void \doxymbox{\hyperlink{stm32u0xx__hal__msp_8c_ae4fb8e66865c87d0ebab74a726a6891f}{HAL\+\_\+\+Msp\+Init}} (void)
\end{DoxyCompactItemize}

\doxysubsection{Detailed Description}
This file provides code for the MSP Initialization and de-\/\+Initialization codes. 

\begin{DoxyAttention}{Attention}

\end{DoxyAttention}
Copyright (c) 2026 STMicroelectronics. All rights reserved.

This software is licensed under terms that can be found in the LICENSE file in the root directory of this software component. If no LICENSE file comes with this software, it is provided AS-\/\+IS. 

\label{stm32u0xx__hal__msp_8c_doc-func-members}
\Hypertarget{stm32u0xx__hal__msp_8c_doc-func-members}
\doxysubsection{Function Documentation}
\Hypertarget{stm32u0xx__hal__msp_8c_ae4fb8e66865c87d0ebab74a726a6891f}\index{stm32u0xx\_hal\_msp.c@{stm32u0xx\_hal\_msp.c}!HAL\_MspInit@{HAL\_MspInit}}
\index{HAL\_MspInit@{HAL\_MspInit}!stm32u0xx\_hal\_msp.c@{stm32u0xx\_hal\_msp.c}}
\doxysubsubsection{\texorpdfstring{HAL\_MspInit()}{HAL\_MspInit()}}
{\footnotesize\ttfamily \label{stm32u0xx__hal__msp_8c_ae4fb8e66865c87d0ebab74a726a6891f} 
void HAL\+\_\+\+Msp\+Init (\begin{DoxyParamCaption}\item[{void}]{}{}\end{DoxyParamCaption})}

Initializes the Global MSP.
