savoirs-vivants/station-analyse-qualite-eau/firmware/Docs/latex/stm32u0xx__it_8h.tex

\doxysection{C:\+/\+\+Users/\+valen/\+\+Documents/\+\+BUT GEII/\+\+SAE601/\+station\+\_\+analyse\+\_\+qualite\+\_\+eau/\+firmware/\+station\+\_\+analyse\+\_\+qualite\+\_\+eau/\+\+Core/\+\+Inc/\+stm32u0xx\+\_\+it.h File Reference}
\hypertarget{stm32u0xx__it_8h}{}\label{stm32u0xx__it_8h}\index{C:/Users/valen/Documents/BUT GEII/SAE601/station\_analyse\_qualite\_eau/firmware/station\_analyse\_qualite\_eau/Core/Inc/stm32u0xx\_it.h@{C:/Users/valen/Documents/BUT GEII/SAE601/station\_analyse\_qualite\_eau/firmware/station\_analyse\_qualite\_eau/Core/Inc/stm32u0xx\_it.h}}

This file contains the headers of the interrupt handlers.  

This graph shows which files directly or indirectly include this file:\+
\nopagebreak
\begin{figure}[H]
\begin{center}
\leavevmode
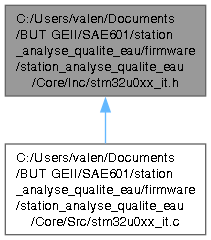
[picture p45: firmware/Docs/html/stm32u0xx__it_8h__dep__incl.png]

\end{center}
\end{figure}
\doxysubsubsection*{Functions}
\begin{DoxyCompactItemize}
\item 
void \doxymbox{\hyperlink{stm32u0xx__it_8h_a6ad7a5e3ee69cb6db6a6b9111ba898bc}{NMI\+\_\+\+Handler}} (void)
\begin{DoxyCompactList}\small\item\em This function handles Non maskable interrupt. \end{DoxyCompactList}\item 
void \doxymbox{\hyperlink{stm32u0xx__it_8h_a2bffc10d5bd4106753b7c30e86903bea}{Hard\+Fault\+\_\+\+Handler}} (void)
\begin{DoxyCompactList}\small\item\em This function handles Hard fault interrupt. \end{DoxyCompactList}\item 
void \doxymbox{\hyperlink{stm32u0xx__it_8h_a3e5ddb3df0d62f2dc357e64a3f04a6ce}{SVC\+\_\+\+Handler}} (void)
\begin{DoxyCompactList}\small\item\em This function handles System service call via SVC instruction. \end{DoxyCompactList}\item 
void \doxymbox{\hyperlink{stm32u0xx__it_8h_a6303e1f258cbdc1f970ce579cc015623}{Pend\+SV\+\_\+\+Handler}} (void)
\begin{DoxyCompactList}\small\item\em This function handles Pendable request for system service. \end{DoxyCompactList}\item 
void \doxymbox{\hyperlink{stm32u0xx__it_8h_ab5e09814056d617c521549e542639b7e}{Sys\+Tick\+\_\+\+Handler}} (void)
\begin{DoxyCompactList}\small\item\em This function handles System tick timer. \end{DoxyCompactList}\item 
void \doxymbox{\hyperlink{stm32u0xx__it_8h_a4818cdec7297513b0645d949e7b8c947}{RTC\+\_\+\+TAMP\+\_\+\+IRQHandler}} (void)
\begin{DoxyCompactList}\small\item\em This function handles RTC and TAMP interrupts (combined EXTI lines 20 \& 21). \end{DoxyCompactList}\item 
void \doxymbox{\hyperlink{stm32u0xx__it_8h_a3595b205bdfadf55a525f2d4f438d122}{EXTI4\+\_\+15\+\_\+\+IRQHandler}} (void)
\begin{DoxyCompactList}\small\item\em This function handles EXTI line 4 to 15 interrupts. \end{DoxyCompactList}\item 
void \doxymbox{\hyperlink{stm32u0xx__it_8h_a7b6fac3d670a4860ebec8a961d5c4a73}{DMA1\+\_\+\+Channel1\+\_\+\+IRQHandler}} (void)
\begin{DoxyCompactList}\small\item\em This function handles DMA1 channel 1 interrupt. \end{DoxyCompactList}\item 
void \doxymbox{\hyperlink{stm32u0xx__it_8h_aedf923a36e99dd50350a393d4e94bc21}{DMA1\+\_\+\+Channel2\+\_\+3\+\_\+\+IRQHandler}} (void)
\begin{DoxyCompactList}\small\item\em This function handles DMA1 channel 2 and channel 3 interrupts. \end{DoxyCompactList}\item 
void \doxymbox{\hyperlink{stm32u0xx__it_8h_a30ff419019b9c90beec6dea34bac776a}{DMA1\+\_\+\+Ch4\+\_\+7\+\_\+\+DMA2\+\_\+\+Ch1\+\_\+5\+\_\+\+DMAMUX\+\_\+\+OVR\+\_\+\+IRQHandler}} (void)
\begin{DoxyCompactList}\small\item\em This function handles DMAMUX\+\_\+\+OVR\+\_\+\+IT + DMA1 channel 4 to 7 + DMA2 channel 1 to 5. \end{DoxyCompactList}\item 
void \doxymbox{\hyperlink{stm32u0xx__it_8h_ad61b08fc2caafdbd427935c39b6f061d}{ADC\+\_\+\+COMP1\+\_\+2\+\_\+\+IRQHandler}} (void)
\begin{DoxyCompactList}\small\item\em This function handles ADC1, COMP1 and COMP2 Interrupts (combined with EXTI 17 \& 18). \end{DoxyCompactList}\item 
void \doxymbox{\hyperlink{stm32u0xx__it_8h_af568806b433e1007e490fe44c7599050}{TIM6\+\_\+\+DAC\+\_\+\+LPTIM1\+\_\+\+IRQHandler}} (void)
\begin{DoxyCompactList}\small\item\em This function handles TIM6, DAC and LPTIM1 global Interrupts (combined with EXTI 31). \end{DoxyCompactList}\item 
void \doxymbox{\hyperlink{stm32u0xx__it_8h_acd68ca5c727a469a63b29aca9de717da}{SPI2\+\_\+3\+\_\+\+IRQHandler}} (void)
\begin{DoxyCompactList}\small\item\em This function handles SPI2 and SPI3 global interrupt. \end{DoxyCompactList}\item 
void \doxymbox{\hyperlink{stm32u0xx__it_8h_ad81f8f5f4eeb37afbe93e95d0727bb73}{USART2\+\_\+\+LPUART2\+\_\+\+IRQHandler}} (void)
\begin{DoxyCompactList}\small\item\em This function handles USART2 global interrupt (combined with EXTI 26) + LPUART2 global interrupt (combined with EXTI lines 35). \end{DoxyCompactList}\item 
void \doxymbox{\hyperlink{stm32u0xx__it_8h_a492d1f59d4204ccb4244427b72c6a540}{USART3\+\_\+\+LPUART1\+\_\+\+IRQHandler}} (void)
\begin{DoxyCompactList}\small\item\em This function handles USART3 (combined with EXTI 24) + LPUART1 global interrupt (combined with EXTI lines 28). \end{DoxyCompactList}\end{DoxyCompactItemize}

\doxysubsection{Detailed Description}
This file contains the headers of the interrupt handlers. 

\begin{DoxyAttention}{Attention}

\end{DoxyAttention}
Copyright (c) 2026 STMicroelectronics. All rights reserved.

This software is licensed under terms that can be found in the LICENSE file in the root directory of this software component. If no LICENSE file comes with this software, it is provided AS-\/\+IS. 

\label{stm32u0xx__it_8h_doc-func-members}
\Hypertarget{stm32u0xx__it_8h_doc-func-members}
\doxysubsection{Function Documentation}
\Hypertarget{stm32u0xx__it_8h_ad61b08fc2caafdbd427935c39b6f061d}\index{stm32u0xx\_it.h@{stm32u0xx\_it.h}!ADC\_COMP1\_2\_IRQHandler@{ADC\_COMP1\_2\_IRQHandler}}
\index{ADC\_COMP1\_2\_IRQHandler@{ADC\_COMP1\_2\_IRQHandler}!stm32u0xx\_it.h@{stm32u0xx\_it.h}}
\doxysubsubsection{\texorpdfstring{ADC\_COMP1\_2\_IRQHandler()}{ADC\_COMP1\_2\_IRQHandler()}}
{\footnotesize\ttfamily \label{stm32u0xx__it_8h_ad61b08fc2caafdbd427935c39b6f061d} 
void ADC\+\_\+\+COMP1\+\_\+2\+\_\+\+IRQHandler (\begin{DoxyParamCaption}\item[{void}]{}{}\end{DoxyParamCaption})}

This function handles ADC1, COMP1 and COMP2 Interrupts (combined with EXTI 17 \& 18). 

\Hypertarget{stm32u0xx__it_8h_a30ff419019b9c90beec6dea34bac776a}\index{stm32u0xx\_it.h@{stm32u0xx\_it.h}!DMA1\_Ch4\_7\_DMA2\_Ch1\_5\_DMAMUX\_OVR\_IRQHandler@{DMA1\_Ch4\_7\_DMA2\_Ch1\_5\_DMAMUX\_OVR\_IRQHandler}}
\index{DMA1\_Ch4\_7\_DMA2\_Ch1\_5\_DMAMUX\_OVR\_IRQHandler@{DMA1\_Ch4\_7\_DMA2\_Ch1\_5\_DMAMUX\_OVR\_IRQHandler}!stm32u0xx\_it.h@{stm32u0xx\_it.h}}
\doxysubsubsection{\texorpdfstring{DMA1\_Ch4\_7\_DMA2\_Ch1\_5\_DMAMUX\_OVR\_IRQHandler()}{DMA1\_Ch4\_7\_DMA2\_Ch1\_5\_DMAMUX\_OVR\_IRQHandler()}}
{\footnotesize\ttfamily \label{stm32u0xx__it_8h_a30ff419019b9c90beec6dea34bac776a} 
void DMA1\+\_\+\+Ch4\+\_\+7\+\_\+\+DMA2\+\_\+\+Ch1\+\_\+5\+\_\+\+DMAMUX\+\_\+\+OVR\+\_\+\+IRQHandler (\begin{DoxyParamCaption}\item[{void}]{}{}\end{DoxyParamCaption})}

This function handles DMAMUX\+\_\+\+OVR\+\_\+\+IT + DMA1 channel 4 to 7 + DMA2 channel 1 to 5. 

\Hypertarget{stm32u0xx__it_8h_a7b6fac3d670a4860ebec8a961d5c4a73}\index{stm32u0xx\_it.h@{stm32u0xx\_it.h}!DMA1\_Channel1\_IRQHandler@{DMA1\_Channel1\_IRQHandler}}
\index{DMA1\_Channel1\_IRQHandler@{DMA1\_Channel1\_IRQHandler}!stm32u0xx\_it.h@{stm32u0xx\_it.h}}
\doxysubsubsection{\texorpdfstring{DMA1\_Channel1\_IRQHandler()}{DMA1\_Channel1\_IRQHandler()}}
{\footnotesize\ttfamily \label{stm32u0xx__it_8h_a7b6fac3d670a4860ebec8a961d5c4a73} 
void DMA1\+\_\+\+Channel1\+\_\+\+IRQHandler (\begin{DoxyParamCaption}\item[{void}]{}{}\end{DoxyParamCaption})}

This function handles DMA1 channel 1 interrupt. 

\Hypertarget{stm32u0xx__it_8h_aedf923a36e99dd50350a393d4e94bc21}\index{stm32u0xx\_it.h@{stm32u0xx\_it.h}!DMA1\_Channel2\_3\_IRQHandler@{DMA1\_Channel2\_3\_IRQHandler}}
\index{DMA1\_Channel2\_3\_IRQHandler@{DMA1\_Channel2\_3\_IRQHandler}!stm32u0xx\_it.h@{stm32u0xx\_it.h}}
\doxysubsubsection{\texorpdfstring{DMA1\_Channel2\_3\_IRQHandler()}{DMA1\_Channel2\_3\_IRQHandler()}}
{\footnotesize\ttfamily \label{stm32u0xx__it_8h_aedf923a36e99dd50350a393d4e94bc21} 
void DMA1\+\_\+\+Channel2\+\_\+3\+\_\+\+IRQHandler (\begin{DoxyParamCaption}\item[{void}]{}{}\end{DoxyParamCaption})}

This function handles DMA1 channel 2 and channel 3 interrupts. 

\Hypertarget{stm32u0xx__it_8h_a3595b205bdfadf55a525f2d4f438d122}\index{stm32u0xx\_it.h@{stm32u0xx\_it.h}!EXTI4\_15\_IRQHandler@{EXTI4\_15\_IRQHandler}}
\index{EXTI4\_15\_IRQHandler@{EXTI4\_15\_IRQHandler}!stm32u0xx\_it.h@{stm32u0xx\_it.h}}
\doxysubsubsection{\texorpdfstring{EXTI4\_15\_IRQHandler()}{EXTI4\_15\_IRQHandler()}}
{\footnotesize\ttfamily \label{stm32u0xx__it_8h_a3595b205bdfadf55a525f2d4f438d122} 
void EXTI4\+\_\+15\+\_\+\+IRQHandler (\begin{DoxyParamCaption}\item[{void}]{}{}\end{DoxyParamCaption})}

This function handles EXTI line 4 to 15 interrupts. 

\Hypertarget{stm32u0xx__it_8h_a2bffc10d5bd4106753b7c30e86903bea}\index{stm32u0xx\_it.h@{stm32u0xx\_it.h}!HardFault\_Handler@{HardFault\_Handler}}
\index{HardFault\_Handler@{HardFault\_Handler}!stm32u0xx\_it.h@{stm32u0xx\_it.h}}
\doxysubsubsection{\texorpdfstring{HardFault\_Handler()}{HardFault\_Handler()}}
{\footnotesize\ttfamily \label{stm32u0xx__it_8h_a2bffc10d5bd4106753b7c30e86903bea} 
void Hard\+Fault\+\_\+\+Handler (\begin{DoxyParamCaption}\item[{void}]{}{}\end{DoxyParamCaption})}

This function handles Hard fault interrupt. 

\Hypertarget{stm32u0xx__it_8h_a6ad7a5e3ee69cb6db6a6b9111ba898bc}\index{stm32u0xx\_it.h@{stm32u0xx\_it.h}!NMI\_Handler@{NMI\_Handler}}
\index{NMI\_Handler@{NMI\_Handler}!stm32u0xx\_it.h@{stm32u0xx\_it.h}}
\doxysubsubsection{\texorpdfstring{NMI\_Handler()}{NMI\_Handler()}}
{\footnotesize\ttfamily \label{stm32u0xx__it_8h_a6ad7a5e3ee69cb6db6a6b9111ba898bc} 
void NMI\+\_\+\+Handler (\begin{DoxyParamCaption}\item[{void}]{}{}\end{DoxyParamCaption})}

This function handles Non maskable interrupt. 

\Hypertarget{stm32u0xx__it_8h_a6303e1f258cbdc1f970ce579cc015623}\index{stm32u0xx\_it.h@{stm32u0xx\_it.h}!PendSV\_Handler@{PendSV\_Handler}}
\index{PendSV\_Handler@{PendSV\_Handler}!stm32u0xx\_it.h@{stm32u0xx\_it.h}}
\doxysubsubsection{\texorpdfstring{PendSV\_Handler()}{PendSV\_Handler()}}
{\footnotesize\ttfamily \label{stm32u0xx__it_8h_a6303e1f258cbdc1f970ce579cc015623} 
void Pend\+SV\+\_\+\+Handler (\begin{DoxyParamCaption}\item[{void}]{}{}\end{DoxyParamCaption})}

This function handles Pendable request for system service. 

\Hypertarget{stm32u0xx__it_8h_a4818cdec7297513b0645d949e7b8c947}\index{stm32u0xx\_it.h@{stm32u0xx\_it.h}!RTC\_TAMP\_IRQHandler@{RTC\_TAMP\_IRQHandler}}
\index{RTC\_TAMP\_IRQHandler@{RTC\_TAMP\_IRQHandler}!stm32u0xx\_it.h@{stm32u0xx\_it.h}}
\doxysubsubsection{\texorpdfstring{RTC\_TAMP\_IRQHandler()}{RTC\_TAMP\_IRQHandler()}}
{\footnotesize\ttfamily \label{stm32u0xx__it_8h_a4818cdec7297513b0645d949e7b8c947} 
void RTC\+\_\+\+TAMP\+\_\+\+IRQHandler (\begin{DoxyParamCaption}\item[{void}]{}{}\end{DoxyParamCaption})}

This function handles RTC and TAMP interrupts (combined EXTI lines 20 \& 21). 

\Hypertarget{stm32u0xx__it_8h_acd68ca5c727a469a63b29aca9de717da}\index{stm32u0xx\_it.h@{stm32u0xx\_it.h}!SPI2\_3\_IRQHandler@{SPI2\_3\_IRQHandler}}
\index{SPI2\_3\_IRQHandler@{SPI2\_3\_IRQHandler}!stm32u0xx\_it.h@{stm32u0xx\_it.h}}
\doxysubsubsection{\texorpdfstring{SPI2\_3\_IRQHandler()}{SPI2\_3\_IRQHandler()}}
{\footnotesize\ttfamily \label{stm32u0xx__it_8h_acd68ca5c727a469a63b29aca9de717da} 
void SPI2\+\_\+3\+\_\+\+IRQHandler (\begin{DoxyParamCaption}\item[{void}]{}{}\end{DoxyParamCaption})}

This function handles SPI2 and SPI3 global interrupt. 

\Hypertarget{stm32u0xx__it_8h_a3e5ddb3df0d62f2dc357e64a3f04a6ce}\index{stm32u0xx\_it.h@{stm32u0xx\_it.h}!SVC\_Handler@{SVC\_Handler}}
\index{SVC\_Handler@{SVC\_Handler}!stm32u0xx\_it.h@{stm32u0xx\_it.h}}
\doxysubsubsection{\texorpdfstring{SVC\_Handler()}{SVC\_Handler()}}
{\footnotesize\ttfamily \label{stm32u0xx__it_8h_a3e5ddb3df0d62f2dc357e64a3f04a6ce} 
void SVC\+\_\+\+Handler (\begin{DoxyParamCaption}\item[{void}]{}{}\end{DoxyParamCaption})}

This function handles System service call via SVC instruction. 

\Hypertarget{stm32u0xx__it_8h_ab5e09814056d617c521549e542639b7e}\index{stm32u0xx\_it.h@{stm32u0xx\_it.h}!SysTick\_Handler@{SysTick\_Handler}}
\index{SysTick\_Handler@{SysTick\_Handler}!stm32u0xx\_it.h@{stm32u0xx\_it.h}}
\doxysubsubsection{\texorpdfstring{SysTick\_Handler()}{SysTick\_Handler()}}
{\footnotesize\ttfamily \label{stm32u0xx__it_8h_ab5e09814056d617c521549e542639b7e} 
void Sys\+Tick\+\_\+\+Handler (\begin{DoxyParamCaption}\item[{void}]{}{}\end{DoxyParamCaption})}

This function handles System tick timer. 

\Hypertarget{stm32u0xx__it_8h_af568806b433e1007e490fe44c7599050}\index{stm32u0xx\_it.h@{stm32u0xx\_it.h}!TIM6\_DAC\_LPTIM1\_IRQHandler@{TIM6\_DAC\_LPTIM1\_IRQHandler}}
\index{TIM6\_DAC\_LPTIM1\_IRQHandler@{TIM6\_DAC\_LPTIM1\_IRQHandler}!stm32u0xx\_it.h@{stm32u0xx\_it.h}}
\doxysubsubsection{\texorpdfstring{TIM6\_DAC\_LPTIM1\_IRQHandler()}{TIM6\_DAC\_LPTIM1\_IRQHandler()}}
{\footnotesize\ttfamily \label{stm32u0xx__it_8h_af568806b433e1007e490fe44c7599050} 
void TIM6\+\_\+\+DAC\+\_\+\+LPTIM1\+\_\+\+IRQHandler (\begin{DoxyParamCaption}\item[{void}]{}{}\end{DoxyParamCaption})}

This function handles TIM6, DAC and LPTIM1 global Interrupts (combined with EXTI 31). 

\Hypertarget{stm32u0xx__it_8h_ad81f8f5f4eeb37afbe93e95d0727bb73}\index{stm32u0xx\_it.h@{stm32u0xx\_it.h}!USART2\_LPUART2\_IRQHandler@{USART2\_LPUART2\_IRQHandler}}
\index{USART2\_LPUART2\_IRQHandler@{USART2\_LPUART2\_IRQHandler}!stm32u0xx\_it.h@{stm32u0xx\_it.h}}
\doxysubsubsection{\texorpdfstring{USART2\_LPUART2\_IRQHandler()}{USART2\_LPUART2\_IRQHandler()}}
{\footnotesize\ttfamily \label{stm32u0xx__it_8h_ad81f8f5f4eeb37afbe93e95d0727bb73} 
void USART2\+\_\+\+LPUART2\+\_\+\+IRQHandler (\begin{DoxyParamCaption}\item[{void}]{}{}\end{DoxyParamCaption})}

This function handles USART2 global interrupt (combined with EXTI 26) + LPUART2 global interrupt (combined with EXTI lines 35). 

\Hypertarget{stm32u0xx__it_8h_a492d1f59d4204ccb4244427b72c6a540}\index{stm32u0xx\_it.h@{stm32u0xx\_it.h}!USART3\_LPUART1\_IRQHandler@{USART3\_LPUART1\_IRQHandler}}
\index{USART3\_LPUART1\_IRQHandler@{USART3\_LPUART1\_IRQHandler}!stm32u0xx\_it.h@{stm32u0xx\_it.h}}
\doxysubsubsection{\texorpdfstring{USART3\_LPUART1\_IRQHandler()}{USART3\_LPUART1\_IRQHandler()}}
{\footnotesize\ttfamily \label{stm32u0xx__it_8h_a492d1f59d4204ccb4244427b72c6a540} 
void USART3\+\_\+\+LPUART1\+\_\+\+IRQHandler (\begin{DoxyParamCaption}\item[{void}]{}{}\end{DoxyParamCaption})}

This function handles USART3 (combined with EXTI 24) + LPUART1 global interrupt (combined with EXTI lines 28).
