savoirs-vivants/station-analyse-qualite-eau/firmware/Docs/latex/stm32u0xx__it_8h_source.tex

\doxysection{stm32u0xx\+\_\+it.\+h}
\hypertarget{stm32u0xx__it_8h_source}{}\label{stm32u0xx__it_8h_source}\index{C:/Users/valen/Documents/BUT GEII/SAE601/station\_analyse\_qualite\_eau/firmware/station\_analyse\_qualite\_eau/Core/Inc/stm32u0xx\_it.h@{C:/Users/valen/Documents/BUT GEII/SAE601/station\_analyse\_qualite\_eau/firmware/station\_analyse\_qualite\_eau/Core/Inc/stm32u0xx\_it.h}}
\doxymbox{\hyperlink{stm32u0xx__it_8h}{Go to the documentation of this file.}}
\begin{DoxyCode}{0}
\DoxyCodeLine{00001\ \textcolor{comment}{/*\ USER\ CODE\ BEGIN\ Header\ */}}
\DoxyCodeLine{00018\ \textcolor{comment}{/*\ USER\ CODE\ END\ Header\ */}}
\DoxyCodeLine{00019\ }
\DoxyCodeLine{00020\ \textcolor{comment}{/*\ Define\ to\ prevent\ recursive\ inclusion\ -\/-\/-\/-\/-\/-\/-\/-\/-\/-\/-\/-\/-\/-\/-\/-\/-\/-\/-\/-\/-\/-\/-\/-\/-\/-\/-\/-\/-\/-\/-\/-\/-\/-\/-\/-\/-\/*/}}
\DoxyCodeLine{00021\ \textcolor{preprocessor}{\#ifndef\ \_\_STM32U0xx\_IT\_H}}
\DoxyCodeLine{00022\ \textcolor{preprocessor}{\#define\ \_\_STM32U0xx\_IT\_H}}
\DoxyCodeLine{00023\ }
\DoxyCodeLine{00024\ \textcolor{preprocessor}{\#ifdef\ \_\_cplusplus}}
\DoxyCodeLine{00025\ \textcolor{keyword}{extern}\ \textcolor{stringliteral}{"{}C"{}}\ \{}
\DoxyCodeLine{00026\ \textcolor{preprocessor}{\#endif}}
\DoxyCodeLine{00027\ }
\DoxyCodeLine{00028\ \textcolor{comment}{/*\ Private\ includes\ -\/-\/-\/-\/-\/-\/-\/-\/-\/-\/-\/-\/-\/-\/-\/-\/-\/-\/-\/-\/-\/-\/-\/-\/-\/-\/-\/-\/-\/-\/-\/-\/-\/-\/-\/-\/-\/-\/-\/-\/-\/-\/-\/-\/-\/-\/-\/-\/-\/-\/-\/-\/-\/-\/-\/-\/-\/-\/*/}}
\DoxyCodeLine{00029\ \textcolor{comment}{/*\ USER\ CODE\ BEGIN\ Includes\ */}}
\DoxyCodeLine{00030\ }
\DoxyCodeLine{00031\ \textcolor{comment}{/*\ USER\ CODE\ END\ Includes\ */}}
\DoxyCodeLine{00032\ }
\DoxyCodeLine{00033\ \textcolor{comment}{/*\ Exported\ types\ -\/-\/-\/-\/-\/-\/-\/-\/-\/-\/-\/-\/-\/-\/-\/-\/-\/-\/-\/-\/-\/-\/-\/-\/-\/-\/-\/-\/-\/-\/-\/-\/-\/-\/-\/-\/-\/-\/-\/-\/-\/-\/-\/-\/-\/-\/-\/-\/-\/-\/-\/-\/-\/-\/-\/-\/-\/-\/-\/-\/*/}}
\DoxyCodeLine{00034\ \textcolor{comment}{/*\ USER\ CODE\ BEGIN\ ET\ */}}
\DoxyCodeLine{00035\ }
\DoxyCodeLine{00036\ \textcolor{comment}{/*\ USER\ CODE\ END\ ET\ */}}
\DoxyCodeLine{00037\ }
\DoxyCodeLine{00038\ \textcolor{comment}{/*\ Exported\ constants\ -\/-\/-\/-\/-\/-\/-\/-\/-\/-\/-\/-\/-\/-\/-\/-\/-\/-\/-\/-\/-\/-\/-\/-\/-\/-\/-\/-\/-\/-\/-\/-\/-\/-\/-\/-\/-\/-\/-\/-\/-\/-\/-\/-\/-\/-\/-\/-\/-\/-\/-\/-\/-\/-\/-\/-\/*/}}
\DoxyCodeLine{00039\ \textcolor{comment}{/*\ USER\ CODE\ BEGIN\ EC\ */}}
\DoxyCodeLine{00040\ }
\DoxyCodeLine{00041\ \textcolor{comment}{/*\ USER\ CODE\ END\ EC\ */}}
\DoxyCodeLine{00042\ }
\DoxyCodeLine{00043\ \textcolor{comment}{/*\ Exported\ macro\ -\/-\/-\/-\/-\/-\/-\/-\/-\/-\/-\/-\/-\/-\/-\/-\/-\/-\/-\/-\/-\/-\/-\/-\/-\/-\/-\/-\/-\/-\/-\/-\/-\/-\/-\/-\/-\/-\/-\/-\/-\/-\/-\/-\/-\/-\/-\/-\/-\/-\/-\/-\/-\/-\/-\/-\/-\/-\/-\/-\/*/}}
\DoxyCodeLine{00044\ \textcolor{comment}{/*\ USER\ CODE\ BEGIN\ EM\ */}}
\DoxyCodeLine{00045\ }
\DoxyCodeLine{00046\ \textcolor{comment}{/*\ USER\ CODE\ END\ EM\ */}}
\DoxyCodeLine{00047\ }
\DoxyCodeLine{00048\ \textcolor{comment}{/*\ Exported\ functions\ prototypes\ -\/-\/-\/-\/-\/-\/-\/-\/-\/-\/-\/-\/-\/-\/-\/-\/-\/-\/-\/-\/-\/-\/-\/-\/-\/-\/-\/-\/-\/-\/-\/-\/-\/-\/-\/-\/-\/-\/-\/-\/-\/-\/-\/-\/-\/*/}}
\DoxyCodeLine{00049\ \textcolor{keywordtype}{void}\ \doxymbox{\hyperlink{stm32u0xx__it_8h_a6ad7a5e3ee69cb6db6a6b9111ba898bc}{NMI\_Handler}}(\textcolor{keywordtype}{void});}
\DoxyCodeLine{00050\ \textcolor{keywordtype}{void}\ \doxymbox{\hyperlink{stm32u0xx__it_8h_a2bffc10d5bd4106753b7c30e86903bea}{HardFault\_Handler}}(\textcolor{keywordtype}{void});}
\DoxyCodeLine{00051\ \textcolor{keywordtype}{void}\ \doxymbox{\hyperlink{stm32u0xx__it_8h_a3e5ddb3df0d62f2dc357e64a3f04a6ce}{SVC\_Handler}}(\textcolor{keywordtype}{void});}
\DoxyCodeLine{00052\ \textcolor{keywordtype}{void}\ \doxymbox{\hyperlink{stm32u0xx__it_8h_a6303e1f258cbdc1f970ce579cc015623}{PendSV\_Handler}}(\textcolor{keywordtype}{void});}
\DoxyCodeLine{00053\ \textcolor{keywordtype}{void}\ \doxymbox{\hyperlink{stm32u0xx__it_8h_ab5e09814056d617c521549e542639b7e}{SysTick\_Handler}}(\textcolor{keywordtype}{void});}
\DoxyCodeLine{00054\ \textcolor{keywordtype}{void}\ \doxymbox{\hyperlink{stm32u0xx__it_8h_a4818cdec7297513b0645d949e7b8c947}{RTC\_TAMP\_IRQHandler}}(\textcolor{keywordtype}{void});}
\DoxyCodeLine{00055\ \textcolor{keywordtype}{void}\ \doxymbox{\hyperlink{stm32u0xx__it_8h_a3595b205bdfadf55a525f2d4f438d122}{EXTI4\_15\_IRQHandler}}(\textcolor{keywordtype}{void});}
\DoxyCodeLine{00056\ \textcolor{keywordtype}{void}\ \doxymbox{\hyperlink{stm32u0xx__it_8h_a7b6fac3d670a4860ebec8a961d5c4a73}{DMA1\_Channel1\_IRQHandler}}(\textcolor{keywordtype}{void});}
\DoxyCodeLine{00057\ \textcolor{keywordtype}{void}\ \doxymbox{\hyperlink{stm32u0xx__it_8h_aedf923a36e99dd50350a393d4e94bc21}{DMA1\_Channel2\_3\_IRQHandler}}(\textcolor{keywordtype}{void});}
\DoxyCodeLine{00058\ \textcolor{keywordtype}{void}\ \doxymbox{\hyperlink{stm32u0xx__it_8h_a30ff419019b9c90beec6dea34bac776a}{DMA1\_Ch4\_7\_DMA2\_Ch1\_5\_DMAMUX\_OVR\_IRQHandler}}(\textcolor{keywordtype}{void});}
\DoxyCodeLine{00059\ \textcolor{keywordtype}{void}\ \doxymbox{\hyperlink{stm32u0xx__it_8h_ad61b08fc2caafdbd427935c39b6f061d}{ADC\_COMP1\_2\_IRQHandler}}(\textcolor{keywordtype}{void});}
\DoxyCodeLine{00060\ \textcolor{keywordtype}{void}\ \doxymbox{\hyperlink{stm32u0xx__it_8h_af568806b433e1007e490fe44c7599050}{TIM6\_DAC\_LPTIM1\_IRQHandler}}(\textcolor{keywordtype}{void});}
\DoxyCodeLine{00061\ \textcolor{keywordtype}{void}\ \doxymbox{\hyperlink{stm32u0xx__it_8h_acd68ca5c727a469a63b29aca9de717da}{SPI2\_3\_IRQHandler}}(\textcolor{keywordtype}{void});}
\DoxyCodeLine{00062\ \textcolor{keywordtype}{void}\ \doxymbox{\hyperlink{stm32u0xx__it_8h_ad81f8f5f4eeb37afbe93e95d0727bb73}{USART2\_LPUART2\_IRQHandler}}(\textcolor{keywordtype}{void});}
\DoxyCodeLine{00063\ \textcolor{keywordtype}{void}\ \doxymbox{\hyperlink{stm32u0xx__it_8h_a492d1f59d4204ccb4244427b72c6a540}{USART3\_LPUART1\_IRQHandler}}(\textcolor{keywordtype}{void});}
\DoxyCodeLine{00064\ \textcolor{comment}{/*\ USER\ CODE\ BEGIN\ EFP\ */}}
\DoxyCodeLine{00065\ }
\DoxyCodeLine{00066\ \textcolor{comment}{/*\ USER\ CODE\ END\ EFP\ */}}
\DoxyCodeLine{00067\ }
\DoxyCodeLine{00068\ \textcolor{preprocessor}{\#ifdef\ \_\_cplusplus}}
\DoxyCodeLine{00069\ \}}
\DoxyCodeLine{00070\ \textcolor{preprocessor}{\#endif}}
\DoxyCodeLine{00071\ }
\DoxyCodeLine{00072\ \textcolor{preprocessor}{\#endif\ }\textcolor{comment}{/*\ \_\_STM32U0xx\_IT\_H\ */}\textcolor{preprocessor}{}}

\end{DoxyCode}
