savoirs-vivants/station-analyse-qualite-eau/firmware/Docs/latex/stm32u0xx__nucleo__conf_8h.tex

\doxysection{C:\+/\+\+Users/\+valen/\+\+Documents/\+\+BUT GEII/\+\+SAE601/\+station\+\_\+analyse\+\_\+qualite\+\_\+eau/\+firmware/\+station\+\_\+analyse\+\_\+qualite\+\_\+eau/\+\+Core/\+\+Inc/\+stm32u0xx\+\_\+nucleo\+\_\+conf.h File Reference}
\hypertarget{stm32u0xx__nucleo__conf_8h}{}\label{stm32u0xx__nucleo__conf_8h}\index{C:/Users/valen/Documents/BUT GEII/SAE601/station\_analyse\_qualite\_eau/firmware/station\_analyse\_qualite\_eau/Core/Inc/stm32u0xx\_nucleo\_conf.h@{C:/Users/valen/Documents/BUT GEII/SAE601/station\_analyse\_qualite\_eau/firmware/station\_analyse\_qualite\_eau/Core/Inc/stm32u0xx\_nucleo\_conf.h}}

STM32\+U0xx\+\_\+\+Nucleo board configuration file. This file should be copied to the application folder and renamed to \doxylink{stm32u0xx__nucleo__conf_8h}{stm32u0xx\+\_\+nucleo\+\_\+conf.\+h}.  

{\ttfamily \+\#include "{}stm32u0xx\+\_\+hal.\+h"{}}\newline
Include dependency graph for stm32u0xx\+\_\+nucleo\+\_\+conf.\+h:\+
\nopagebreak
\begin{figure}[H]
\begin{center}
\leavevmode
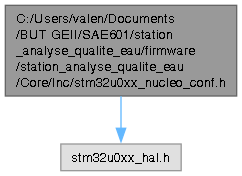
[picture p46: firmware/Docs/html/stm32u0xx__nucleo__conf_8h__incl.png]

\end{center}
\end{figure}
\doxysubsubsection*{Macros}
\begin{DoxyCompactItemize}
\item 
\+\#define \doxymbox{\hyperlink{group___s_t_m32_u0_x_x___n_u_c_l_e_o___c_o_n_f_i_g___exported___constants_ga1c904759ca0f0f958425feb6423db4c0}{USE\+\_\+\+STM32\+U0\+XX\+\_\+\+NUCLEO}}
\item 
\+\#define \doxymbox{\hyperlink{group___s_t_m32_u0_x_x___n_u_c_l_e_o___c_o_n_f_i_g___exported___constants_gae4e30044c77234f9c00f69ece2b417df}{USE\+\_\+\+COM\+\_\+\+LOG}}~1U
\item
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
