savoirs-vivants/station-analyse-qualite-eau/hardware/3D_Models/744031004.stp

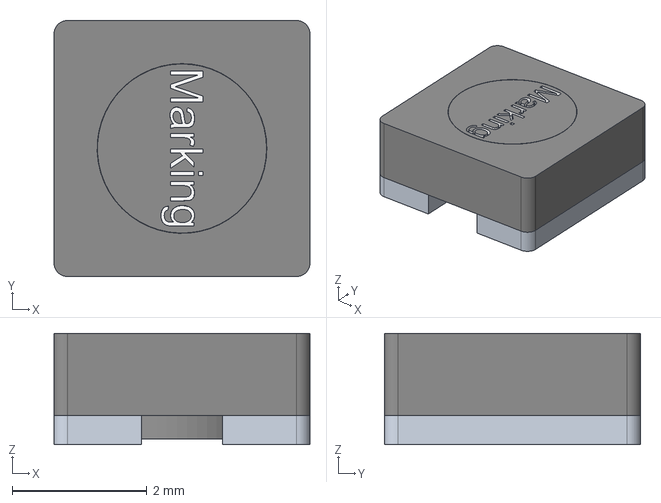
[picture p62: CAD file, 2026-06-05]
hardware/3D_Models/744031004.stp
3.80 x 3.80 x 1.65 mm
