savoirs-vivants/station-analyse-qualite-eau/firmware/Docs/latex/test__analog_8h__incl.pdf

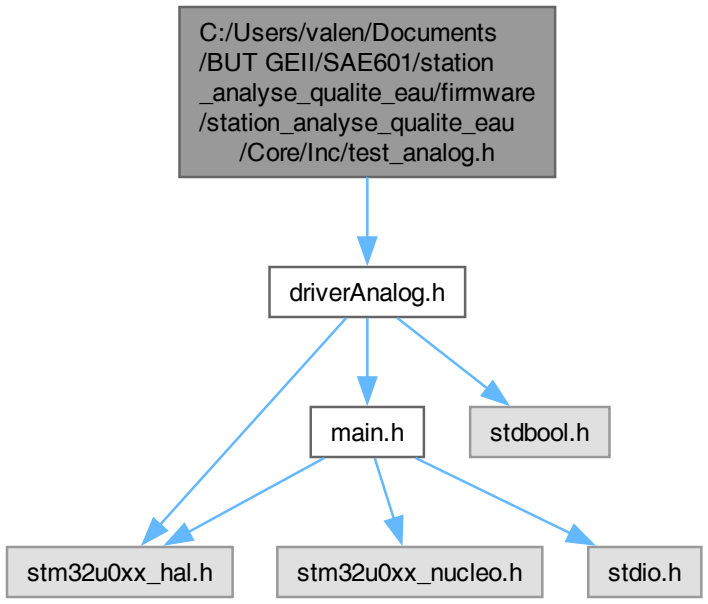
[picture p64: figure]
C:/Users/valen/Documents /BUT GEII/SAE601/station _analyse_qualite_eau/firmware /station_analyse_qualite_eau /Core/Inc/test_analog.h; driverAnalog.h; main.h; stm32u0xx_hal.h; stdbool.h; stm32u0xx_nucleo.h; stdio.h
