savoirs-vivants/station-analyse-qualite-eau/firmware/Docs/latex/test__ble_8c__incl.pdf

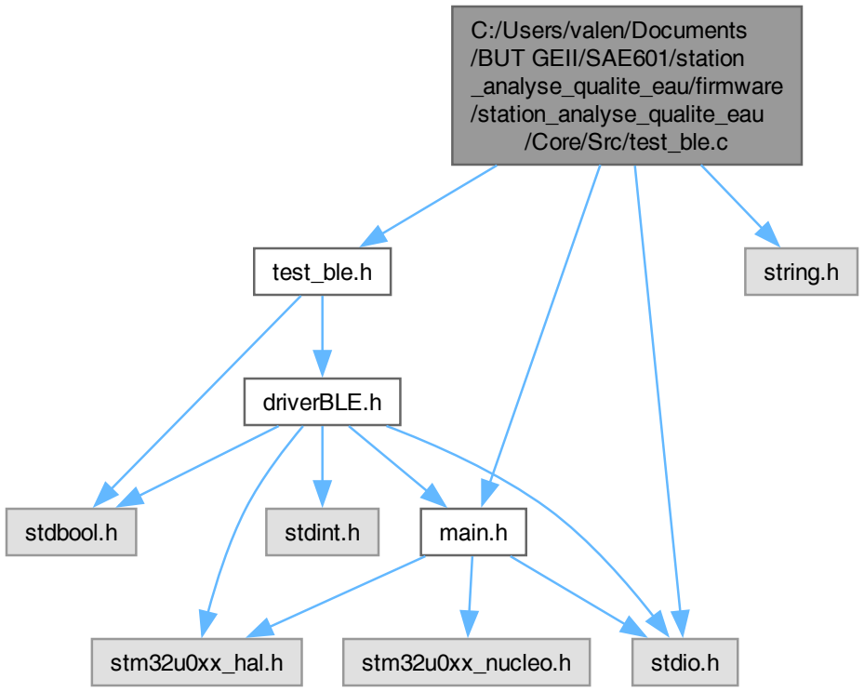
[picture p65: figure]
C:/Users/valen/Documents /BUT GEII/SAE601/station _analyse_qualite_eau/firmware /station_analyse_qualite_eau /Core/Src/test_ble.c; test_ble.h; main.h; stdio.h; string.h; driverBLE.h; stdbool.h; stdint.h; stm32u0xx_hal.h; stm32u0xx_nucleo.h
