savoirs-vivants/station-analyse-qualite-eau/firmware/Docs/latex/test__datalog_8h__incl.pdf

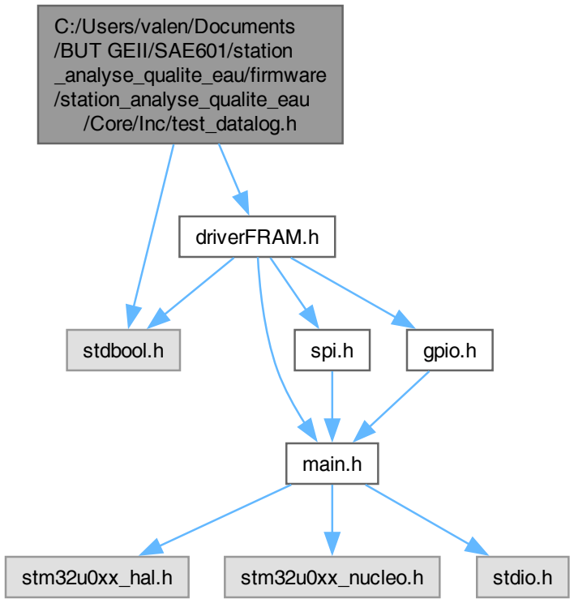
[picture p67: figure]
C:/Users/valen/Documents /BUT GEII/SAE601/station _analyse_qualite_eau/firmware /station_analyse_qualite_eau /Core/Inc/test_datalog.h; stdbool.h; driverFRAM.h; main.h; spi.h; gpio.h; stm32u0xx_hal.h; stm32u0xx_nucleo.h; stdio.h
