savoirs-vivants/station-analyse-qualite-eau/firmware/Docs/latex/test__ds18b20_8c__incl.pdf

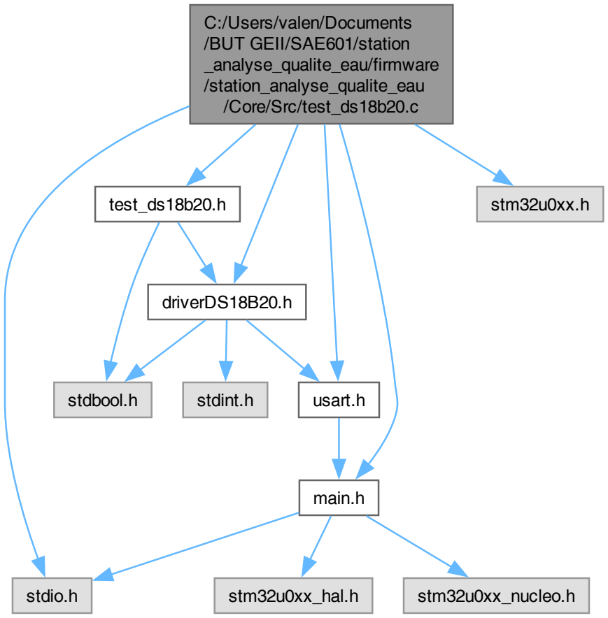
[picture p68: figure]
C:/Users/valen/Documents /BUT GEII/SAE601/station _analyse_qualite_eau/firmware /station_analyse_qualite_eau /Core/Src/test_ds18b20.c; stdio.h; test_ds18b20.h; driverDS18B20.h; usart.h; main.h; stm32u0xx.h; stdbool.h; stdint.h; stm32u0xx_hal.h; stm32u0xx_nucleo.h
