savoirs-vivants/station-analyse-qualite-eau/firmware/Docs/latex/test__ds18b20_8h__incl.pdf

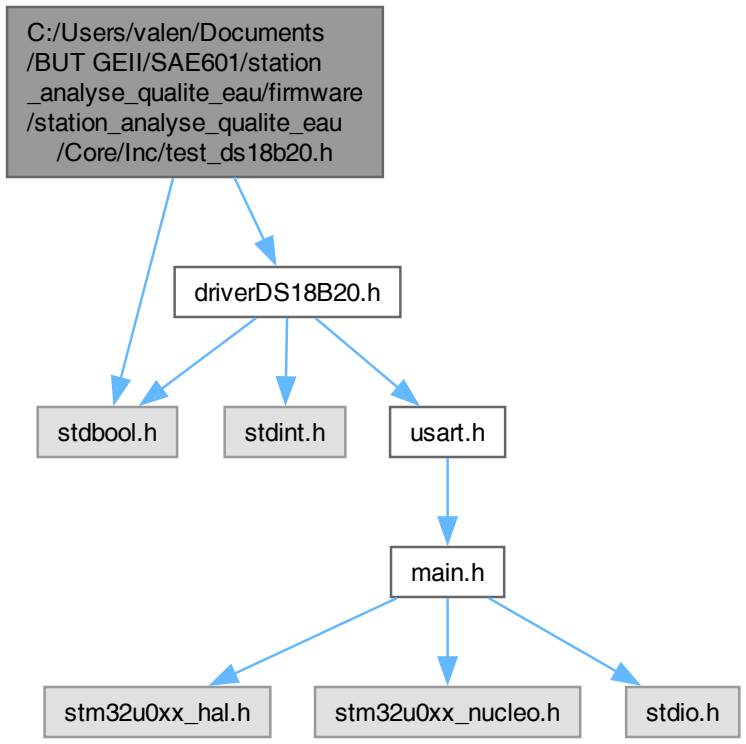
[picture p69: figure]
C:/Users/valen/Documents /BUT GEII/SAE601/station _analyse_qualite_eau/firmware /station_analyse_qualite_eau /Core/Inc/test_ds18b20.h; stdbool.h; driverDS18B20.h; stdint.h; usart.h; main.h; stm32u0xx_hal.h; stm32u0xx_nucleo.h; stdio.h
