savoirs-vivants/station-analyse-qualite-eau/firmware/Docs/latex/test__fram_8c__incl.pdf

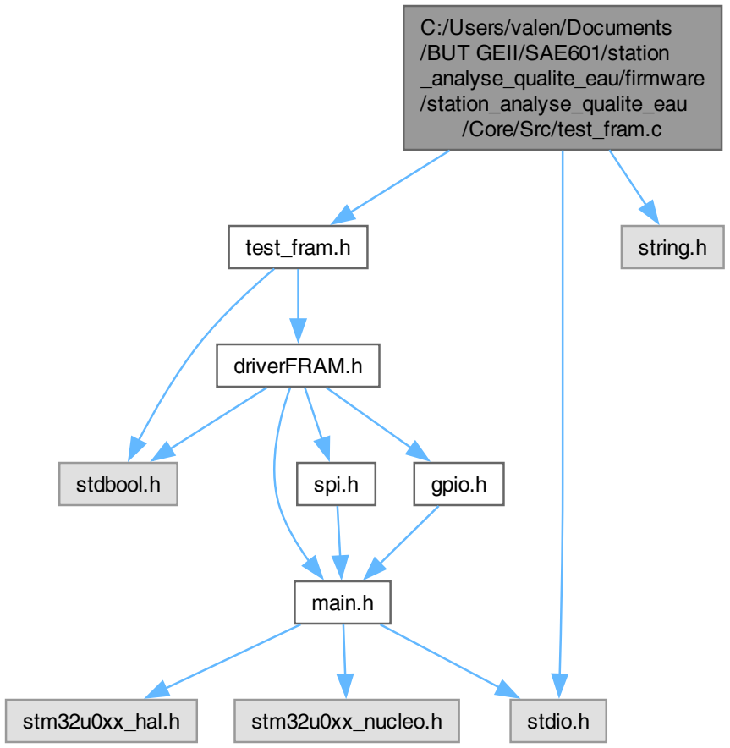
[picture p70: figure]
C:/Users/valen/Documents /BUT GEII/SAE601/station _analyse_qualite_eau/firmware /station_analyse_qualite_eau /Core/Src/test_fram.c; test_fram.h; stdio.h; string.h; stdbool.h; driverFRAM.h; main.h; spi.h; gpio.h; stm32u0xx_hal.h; stm32u0xx_nucleo.h
