savoirs-vivants/station-analyse-qualite-eau/firmware/Docs/latex/test__fram_8h__incl.pdf

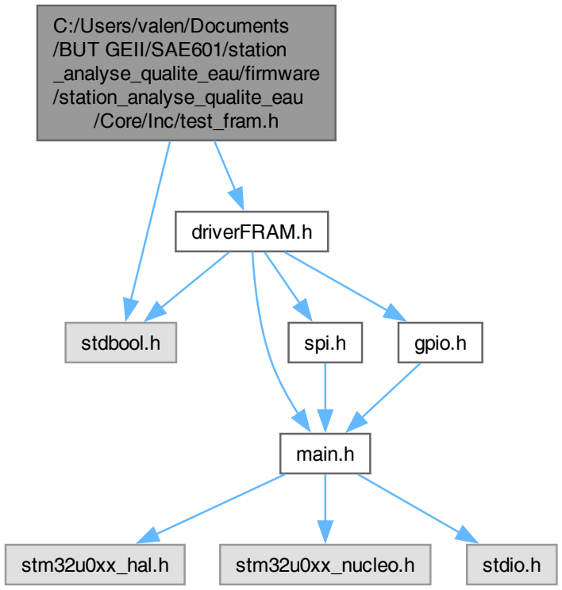
[picture p71: figure]
C:/Users/valen/Documents /BUT GEII/SAE601/station _analyse_qualite_eau/firmware /station_analyse_qualite_eau /Core/Inc/test_fram.h; stdbool.h; driverFRAM.h; main.h; spi.h; gpio.h; stm32u0xx_hal.h; stm32u0xx_nucleo.h; stdio.h
