savoirs-vivants/station-analyse-qualite-eau/firmware/Docs/latex/test__lorawan_8c__incl.pdf

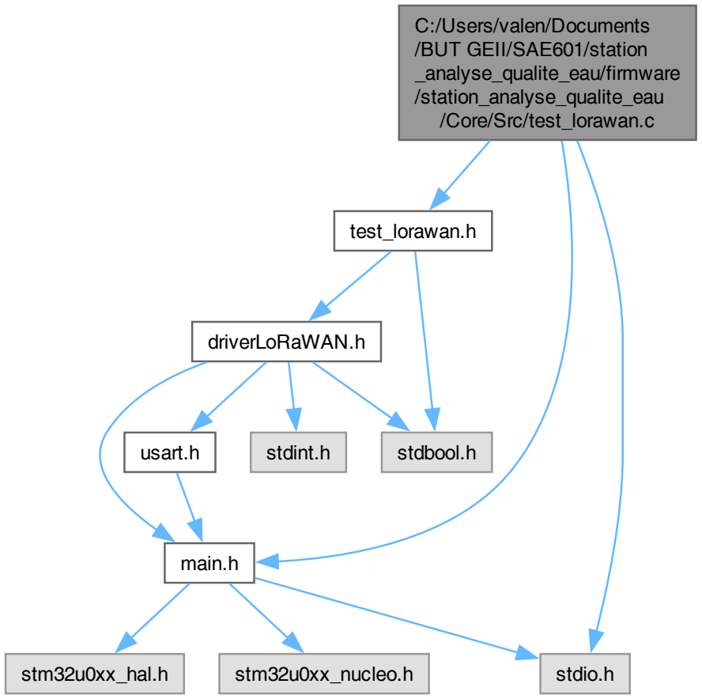
[picture p72: figure]
C:/Users/valen/Documents /BUT GEII/SAE601/station _analyse_qualite_eau/firmware /station_analyse_qualite_eau /Core/Src/test_lorawan.c; test_lorawan.h; main.h; stdio.h; driverLoRaWAN.h; usart.h; stdint.h; stdbool.h; stm32u0xx_hal.h; stm32u0xx_nucleo.h
