savoirs-vivants/station-analyse-qualite-eau/firmware/Docs/latex/test__lorawan_8h__incl.pdf

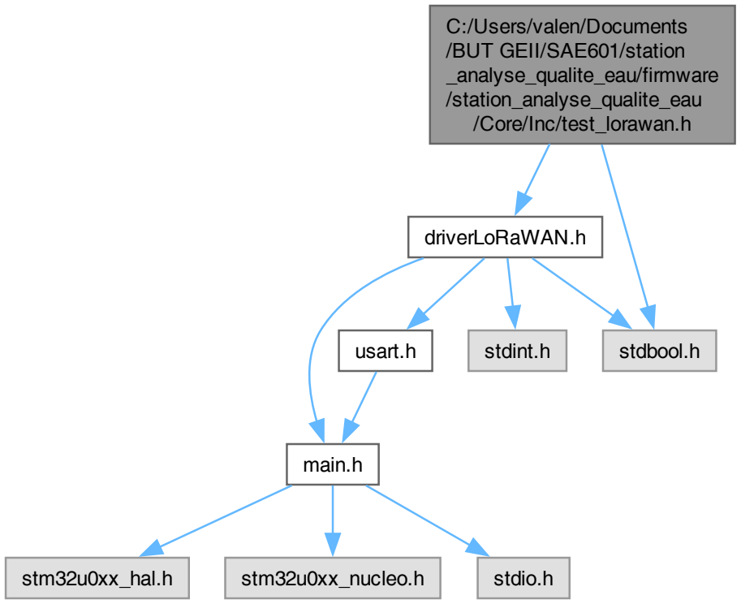
[picture p73: figure]
C:/Users/valen/Documents /BUT GEII/SAE601/station _analyse_qualite_eau/firmware /station_analyse_qualite_eau /Core/Inc/test_lorawan.h; driverLoRaWAN.h; stdbool.h; main.h; usart.h; stdint.h; stm32u0xx_hal.h; stm32u0xx_nucleo.h; stdio.h
