savoirs-vivants/station-analyse-qualite-eau/firmware/Docs/latex/test__lpp_8c__incl.pdf

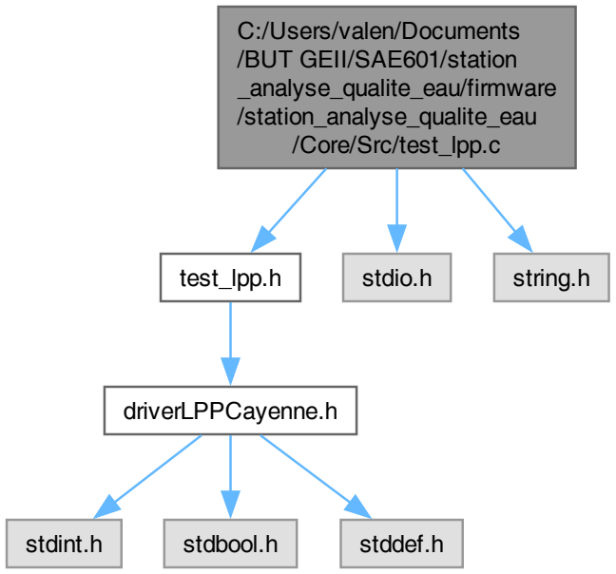
[picture p74: figure]
C:/Users/valen/Documents /BUT GEII/SAE601/station _analyse_qualite_eau/firmware /station_analyse_qualite_eau /Core/Src/test_lpp.c; test_lpp.h; stdio.h; string.h; driverLPPCayenne.h; stdint.h; stdbool.h; stddef.h
