savoirs-vivants/station-analyse-qualite-eau/firmware/Docs/latex/test__lpp_8h__incl.pdf

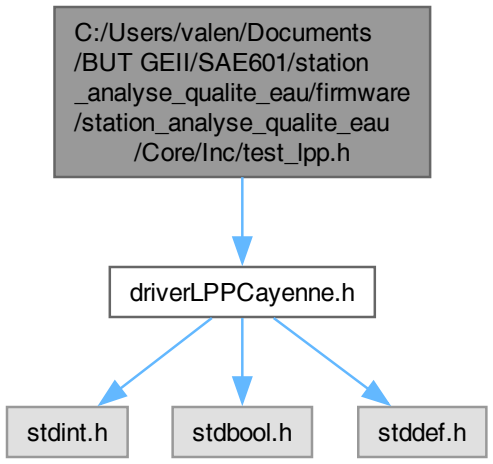
[picture p75: figure]
C:/Users/valen/Documents /BUT GEII/SAE601/station _analyse_qualite_eau/firmware /station_analyse_qualite_eau /Core/Inc/test_lpp.h; driverLPPCayenne.h; stdint.h; stdbool.h; stddef.h
