savoirs-vivants/station-analyse-qualite-eau/firmware/Docs/latex/test__ds18b20_8h.tex

\doxysection{C:\+/\+\+Users/\+valen/\+\+Documents/\+\+BUT GEII/\+\+SAE601/\+station\+\_\+analyse\+\_\+qualite\+\_\+eau/\+firmware/\+station\+\_\+analyse\+\_\+qualite\+\_\+eau/\+\+Core/\+\+Inc/\+test\+\_\+ds18b20.h File Reference}
\hypertarget{test__ds18b20_8h}{}\label{test__ds18b20_8h}\index{C:/Users/valen/Documents/BUT GEII/SAE601/station\_analyse\_qualite\_eau/firmware/station\_analyse\_qualite\_eau/Core/Inc/test\_ds18b20.h@{C:/Users/valen/Documents/BUT GEII/SAE601/station\_analyse\_qualite\_eau/firmware/station\_analyse\_qualite\_eau/Core/Inc/test\_ds18b20.h}}
{\ttfamily \+\#include $<$stdbool.\+h$>$}\newline
{\ttfamily \+\#include "{}driver\+DS18\+B20.\+h"{}}\newline
Include dependency graph for test\+\_\+ds18b20.\+h:\+
\nopagebreak
\begin{figure}[H]
\begin{center}
\leavevmode
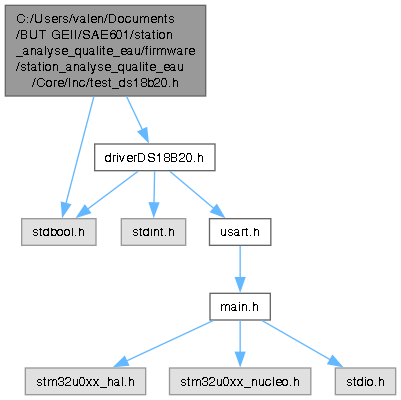
[picture p91: firmware/Docs/html/test__ds18b20_8h__incl.png]

\end{center}
\end{figure}
This graph shows which files directly or indirectly include this file:\+
\nopagebreak
\begin{figure}[H]
\begin{center}
\leavevmode
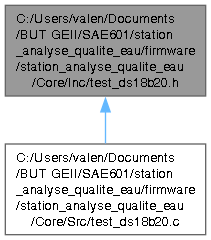
[picture p92: firmware/Docs/html/test__ds18b20_8h__dep__incl.png]

\end{center}
\end{figure}
\doxysubsubsection*{Functions}
\begin{DoxyCompactItemize}
\item 
bool \doxymbox{\hyperlink{test__ds18b20_8h_a3b53a1ac5f4c7371f692d110e37484cd}{Test\+DS18\+B20\+\_\+\+Run\+All}} (\doxymbox{\hyperlink{struct_d_s18_b20__t}{DS18\+B20\+\_\+t}} \texorpdfstring{$\ast$}{*}hds)
\end{DoxyCompactItemize}

\label{test__ds18b20_8h_doc-func-members}
\Hypertarget{test__ds18b20_8h_doc-func-members}
\doxysubsection{Function Documentation}
\Hypertarget{test__ds18b20_8h_a3b53a1ac5f4c7371f692d110e37484cd}\index{test\_ds18b20.h@{test\_ds18b20.h}!TestDS18B20\_RunAll@{TestDS18B20\_RunAll}}
\index{TestDS18B20\_RunAll@{TestDS18B20\_RunAll}!test\_ds18b20.h@{test\_ds18b20.h}}
\doxysubsubsection{\texorpdfstring{TestDS18B20\_RunAll()}{TestDS18B20\_RunAll()}}
{\footnotesize\ttfamily \label{test__ds18b20_8h_a3b53a1ac5f4c7371f692d110e37484cd} 
bool Test\+DS18\+B20\+\_\+\+Run\+All (\begin{DoxyParamCaption}\item[{\doxymbox{\hyperlink{struct_d_s18_b20__t}{DS18\+B20\+\_\+t}} \texorpdfstring{$\ast$}{*}}]{hds}{}\end{DoxyParamCaption})}

Here is the caller graph for this function:\+
\nopagebreak
\begin{figure}[H]
\begin{center}
\leavevmode

\end{center}
\end{figure}
