savoirs-vivants/station-analyse-qualite-eau/firmware/Docs/latex/test__fram_8c.tex

\doxysection{C:\+/\+\+Users/\+valen/\+\+Documents/\+\+BUT GEII/\+\+SAE601/\+station\+\_\+analyse\+\_\+qualite\+\_\+eau/\+firmware/\+station\+\_\+analyse\+\_\+qualite\+\_\+eau/\+\+Core/\+\+Src/\+test\+\_\+fram.c File Reference}
\hypertarget{test__fram_8c}{}\label{test__fram_8c}\index{C:/Users/valen/Documents/BUT GEII/SAE601/station\_analyse\_qualite\_eau/firmware/station\_analyse\_qualite\_eau/Core/Src/test\_fram.c@{C:/Users/valen/Documents/BUT GEII/SAE601/station\_analyse\_qualite\_eau/firmware/station\_analyse\_qualite\_eau/Core/Src/test\_fram.c}}
{\ttfamily \+\#include "{}test\+\_\+fram.\+h"{}}\newline
{\ttfamily \+\#include $<$stdio.\+h$>$}\newline
{\ttfamily \+\#include $<$string.\+h$>$}\newline
Include dependency graph for test\+\_\+fram.\+c:\+
\nopagebreak
\begin{figure}[H]
\begin{center}
\leavevmode
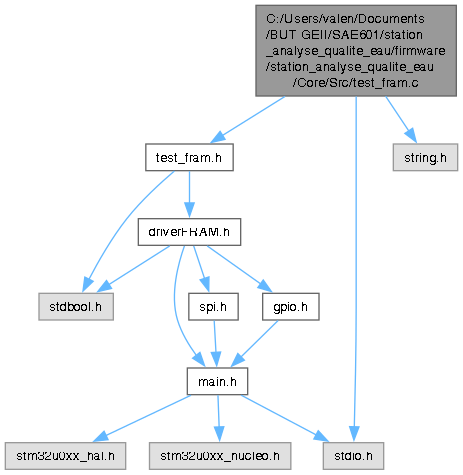
[picture p93: firmware/Docs/html/test__fram_8c__incl.png]

\end{center}
\end{figure}
\doxysubsubsection*{Macros}
\begin{DoxyCompactItemize}
\item 
\+\#define \doxymbox{\hyperlink{test__fram_8c_a2ddacbe405fe687f6fb48cdcbebf2f3b}{EXPECT}}(cond,  msg)
\item 
\+\#define \doxymbox{\hyperlink{test__fram_8c_a6ffea8cdf1ef4b07935b62dc59d009db}{EXPECT\+\_\+\+EQ}}(actual,  expected,  msg)
\end{DoxyCompactItemize}
\doxysubsubsection*{Functions}
\begin{DoxyCompactItemize}
\item 
bool \doxymbox{\hyperlink{test__fram_8c_ae5fb778889b60b9f94b1ec5c71727c81}{Test\+FRAM\+\_\+\+Run\+All}} (\doxymbox{\hyperlink{struct_f_r_a_m__t}{FRAM\+\_\+t}} \texorpdfstring{$\ast$}{*}hfram)
\begin{DoxyCompactList}\small\item\em Lance toute la batterie de tests sur la FRAM. \end{DoxyCompactList}\end{DoxyCompactItemize}

\label{test__fram_8c_doc-define-members}
\Hypertarget{test__fram_8c_doc-define-members}
\doxysubsection{Macro Definition Documentation}
\Hypertarget{test__fram_8c_a2ddacbe405fe687f6fb48cdcbebf2f3b}\index{test\_fram.c@{test\_fram.c}!EXPECT@{EXPECT}}
\index{EXPECT@{EXPECT}!test\_fram.c@{test\_fram.c}}
\doxysubsubsection{\texorpdfstring{EXPECT}{EXPECT}}
{\footnotesize\ttfamily \label{test__fram_8c_a2ddacbe405fe687f6fb48cdcbebf2f3b} 
\+\#define EXPECT(\begin{DoxyParamCaption}\item[{}]{cond}{, }\item[{}]{msg}{}\end{DoxyParamCaption})}

{\bfseries Value:\+}
\begin{DoxyCode}{0}
\DoxyCodeLine{\textcolor{keywordflow}{do}\ \{\ \ \ \ \ \ \ \ \ \ \ \ \ \ \ \ \ \ \ \ \ \ \ \ \ \ \ \ \ \ \ \ \ \ \ \ \ \ \ \ \ \ \ \ \ \ \ \ \ \ \ \ \ \ \ \ \ \ \ \ \(\backslash\)}
\DoxyCodeLine{\ \ \ \ if\ (!(cond))\ \{\ \ \ \ \ \ \ \ \ \ \ \ \ \ \ \ \ \ \ \ \ \ \ \ \ \ \ \ \ \ \ \ \ \ \ \ \ \ \ \ \ \ \ \ \ \ \(\backslash\)}
\DoxyCodeLine{\ \ \ \ \ \ \ \ printf(\textcolor{stringliteral}{"{}\ \ [FAIL]\ \%s\ (ligne\ \%d)\(\backslash\)r\(\backslash\)n"{}},\ msg,\ \_\_LINE\_\_);\ \ \ \ \(\backslash\)}
\DoxyCodeLine{\ \ \ \ \ \ \ \ \textcolor{keywordflow}{return}\ \textcolor{keyword}{false};\ \ \ \ \ \ \ \ \ \ \ \ \ \ \ \ \ \ \ \ \ \ \ \ \ \ \ \ \ \ \ \ \ \ \ \ \ \ \ \ \ \ \ \(\backslash\)}
\DoxyCodeLine{\ \ \ \ \}\ \textcolor{keywordflow}{else}\ \{\ \ \ \ \ \ \ \ \ \ \ \ \ \ \ \ \ \ \ \ \ \ \ \ \ \ \ \ \ \ \ \ \ \ \ \ \ \ \ \ \ \ \ \ \ \ \ \ \ \ \ \ \(\backslash\)}
\DoxyCodeLine{\ \ \ \ \ \ \ \ printf(\textcolor{stringliteral}{"{}\ \ [\ OK\ ]\ \%s\(\backslash\)r\(\backslash\)n"{}},\ msg);\ \ \ \ \ \ \ \ \ \ \ \ \ \ \ \ \ \ \ \ \ \ \ \ \ \(\backslash\)}
\DoxyCodeLine{\ \ \ \ \}\ \ \ \ \ \ \ \ \ \ \ \ \ \ \ \ \ \ \ \ \ \ \ \ \ \ \ \ \ \ \ \ \ \ \ \ \ \ \ \ \ \ \ \ \ \ \ \ \ \ \ \ \ \ \ \ \ \ \ \(\backslash\)}
\DoxyCodeLine{\}\ \textcolor{keywordflow}{while}\ (0)}

\end{DoxyCode}
\Hypertarget{test__fram_8c_a6ffea8cdf1ef4b07935b62dc59d009db}\index{test\_fram.c@{test\_fram.c}!EXPECT\_EQ@{EXPECT\_EQ}}
\index{EXPECT\_EQ@{EXPECT\_EQ}!test\_fram.c@{test\_fram.c}}
\doxysubsubsection{\texorpdfstring{EXPECT\_EQ}{EXPECT\_EQ}}
{\footnotesize\ttfamily \label{test__fram_8c_a6ffea8cdf1ef4b07935b62dc59d009db} 
\+\#define EXPECT\+\_\+\+EQ(\begin{DoxyParamCaption}\item[{}]{actual}{, }\item[{}]{expected}{, }\item[{}]{msg}{}\end{DoxyParamCaption})}

{\bfseries Value:\+}
\begin{DoxyCode}{0}
\DoxyCodeLine{\textcolor{keywordflow}{do}\ \{\ \ \ \ \ \ \ \ \ \ \ \ \ \ \ \ \ \ \ \ \ \ \ \ \ \ \ \ \ \ \ \ \ \ \ \ \ \ \ \ \ \ \ \ \ \ \ \ \ \ \ \ \ \ \ \ \ \ \ \ \ \ \ \ \ \ \ \ \(\backslash\)}
\DoxyCodeLine{\ \ \ \ uint32\_t\ \_a\ =\ (uint32\_t)(actual);\ \ \ \ \ \ \ \ \ \ \ \ \ \ \ \ \ \ \ \ \ \ \ \ \ \ \ \ \ \ \ \ \ \ \ \(\backslash\)}
\DoxyCodeLine{\ \ \ \ uint32\_t\ \_e\ =\ (uint32\_t)(expected);\ \ \ \ \ \ \ \ \ \ \ \ \ \ \ \ \ \ \ \ \ \ \ \ \ \ \ \ \ \ \ \ \ \(\backslash\)}
\DoxyCodeLine{\ \ \ \ if\ (\_a\ !=\ \_e)\ \{\ \ \ \ \ \ \ \ \ \ \ \ \ \ \ \ \ \ \ \ \ \ \ \ \ \ \ \ \ \ \ \ \ \ \ \ \ \ \ \ \ \ \ \ \ \ \ \ \ \ \ \ \ \(\backslash\)}
\DoxyCodeLine{\ \ \ \ \ \ \ \ printf(\textcolor{stringliteral}{"{}\ \ [FAIL]\ \%s\ -\/\ Attendu:\ \%lu,\ Recu:\ \%lu\ (ligne\ \%d)\(\backslash\)r\(\backslash\)n"{}},\ \ \(\backslash\)}
\DoxyCodeLine{\ \ \ \ \ \ \ \ \ \ \ \ \ \ \ msg,\ (\textcolor{keywordtype}{unsigned}\ \textcolor{keywordtype}{long})\_e,\ (\textcolor{keywordtype}{unsigned}\ \textcolor{keywordtype}{long})\_a,\ \_\_LINE\_\_);\ \ \ \ \(\backslash\)}
\DoxyCodeLine{\ \ \ \ \ \ \ \ \textcolor{keywordflow}{return}\ \textcolor{keyword}{false};\ \ \ \ \ \ \ \ \ \ \ \ \ \ \ \ \ \ \ \ \ \ \ \ \ \ \ \ \ \ \ \ \ \ \ \ \ \ \ \ \ \ \ \ \ \ \ \ \ \ \ \(\backslash\)}
\DoxyCodeLine{\ \ \ \ \}\ \textcolor{keywordflow}{else}\ \{\ \ \ \ \ \ \ \ \ \ \ \ \ \ \ \ \ \ \ \ \ \ \ \ \ \ \ \ \ \ \ \ \ \ \ \ \ \ \ \ \ \ \ \ \ \ \ \ \ \ \ \ \ \ \ \ \ \ \ \ \(\backslash\)}
\DoxyCodeLine{\ \ \ \ \ \ \ \ printf(\textcolor{stringliteral}{"{}\ \ [\ OK\ ]\ \%s\(\backslash\)r\(\backslash\)n"{}},\ msg);\ \ \ \ \ \ \ \ \ \ \ \ \ \ \ \ \ \ \ \ \ \ \ \ \ \ \ \ \ \ \ \ \ \(\backslash\)}
\DoxyCodeLine{\ \ \ \ \}\ \ \ \ \ \ \ \ \ \ \ \ \ \ \ \ \ \ \ \ \ \ \ \ \ \ \ \ \ \ \ \ \ \ \ \ \ \ \ \ \ \ \ \ \ \ \ \ \ \ \ \ \ \ \ \ \ \ \ \ \ \ \ \ \ \ \ \(\backslash\)}
\DoxyCodeLine{\}\ \textcolor{keywordflow}{while}\ (0)}

\end{DoxyCode}

\label{test__fram_8c_doc-func-members}
\Hypertarget{test__fram_8c_doc-func-members}
\doxysubsection{Function Documentation}
\Hypertarget{test__fram_8c_ae5fb778889b60b9f94b1ec5c71727c81}\index{test\_fram.c@{test\_fram.c}!TestFRAM\_RunAll@{TestFRAM\_RunAll}}
\index{TestFRAM\_RunAll@{TestFRAM\_RunAll}!test\_fram.c@{test\_fram.c}}
\doxysubsubsection{\texorpdfstring{TestFRAM\_RunAll()}{TestFRAM\_RunAll()}}
{\footnotesize\ttfamily \label{test__fram_8c_ae5fb778889b60b9f94b1ec5c71727c81} 
bool Test\+FRAM\+\_\+\+Run\+All (\begin{DoxyParamCaption}\item[{\doxymbox{\hyperlink{struct_f_r_a_m__t}{FRAM\+\_\+t}} \texorpdfstring{$\ast$}{*}}]{hfram}{}\end{DoxyParamCaption})}

Lance toute la batterie de tests sur la FRAM. 

\begin{DoxyParams}{Parameters}
{\em hfram} & Pointeur vers le handle FRAM initialisé. \\
\hline
\end{DoxyParams}
\begin{DoxyReturn}{Returns}
true si tous les tests passent, false sinon. 
\end{DoxyReturn}
Here is the caller graph for this function:\+
\nopagebreak
\begin{figure}[H]
\begin{center}
\leavevmode

\end{center}
\end{figure}
