savoirs-vivants/station-analyse-qualite-eau/firmware/Docs/latex/test__fram_8h.tex

\doxysection{C:\+/\+\+Users/\+valen/\+\+Documents/\+\+BUT GEII/\+\+SAE601/\+station\+\_\+analyse\+\_\+qualite\+\_\+eau/\+firmware/\+station\+\_\+analyse\+\_\+qualite\+\_\+eau/\+\+Core/\+\+Inc/\+test\+\_\+fram.h File Reference}
\hypertarget{test__fram_8h}{}\label{test__fram_8h}\index{C:/Users/valen/Documents/BUT GEII/SAE601/station\_analyse\_qualite\_eau/firmware/station\_analyse\_qualite\_eau/Core/Inc/test\_fram.h@{C:/Users/valen/Documents/BUT GEII/SAE601/station\_analyse\_qualite\_eau/firmware/station\_analyse\_qualite\_eau/Core/Inc/test\_fram.h}}
{\ttfamily \+\#include $<$stdbool.\+h$>$}\newline
{\ttfamily \+\#include "{}driver\+FRAM.\+h"{}}\newline
Include dependency graph for test\+\_\+fram.\+h:\+
\nopagebreak
\begin{figure}[H]
\begin{center}
\leavevmode
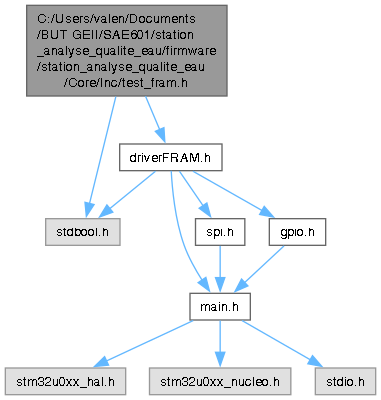
[picture p94: firmware/Docs/html/test__fram_8h__incl.png]

\end{center}
\end{figure}
This graph shows which files directly or indirectly include this file:\+
\nopagebreak
\begin{figure}[H]
\begin{center}
\leavevmode
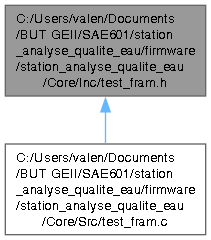
[picture p95: firmware/Docs/html/test__fram_8h__dep__incl.png]

\end{center}
\end{figure}
\doxysubsubsection*{Functions}
\begin{DoxyCompactItemize}
\item 
bool \doxymbox{\hyperlink{test__fram_8h_ae5fb778889b60b9f94b1ec5c71727c81}{Test\+FRAM\+\_\+\+Run\+All}} (\doxymbox{\hyperlink{struct_f_r_a_m__t}{FRAM\+\_\+t}} \texorpdfstring{$\ast$}{*}hfram)
\begin{DoxyCompactList}\small\item\em Lance toute la batterie de tests sur la FRAM. \end{DoxyCompactList}\end{DoxyCompactItemize}

\label{test__fram_8h_doc-func-members}
\Hypertarget{test__fram_8h_doc-func-members}
\doxysubsection{Function Documentation}
\Hypertarget{test__fram_8h_ae5fb778889b60b9f94b1ec5c71727c81}\index{test\_fram.h@{test\_fram.h}!TestFRAM\_RunAll@{TestFRAM\_RunAll}}
\index{TestFRAM\_RunAll@{TestFRAM\_RunAll}!test\_fram.h@{test\_fram.h}}
\doxysubsubsection{\texorpdfstring{TestFRAM\_RunAll()}{TestFRAM\_RunAll()}}
{\footnotesize\ttfamily \label{test__fram_8h_ae5fb778889b60b9f94b1ec5c71727c81} 
bool Test\+FRAM\+\_\+\+Run\+All (\begin{DoxyParamCaption}\item[{\doxymbox{\hyperlink{struct_f_r_a_m__t}{FRAM\+\_\+t}} \texorpdfstring{$\ast$}{*}}]{hfram}{}\end{DoxyParamCaption})}

Lance toute la batterie de tests sur la FRAM. 

\begin{DoxyParams}{Parameters}
{\em hfram} & Pointeur vers le handle FRAM initialisé. \\
\hline
\end{DoxyParams}
\begin{DoxyReturn}{Returns}
true si tous les tests passent, false sinon. 
\end{DoxyReturn}
Here is the caller graph for this function:\+
\nopagebreak
\begin{figure}[H]
\begin{center}
\leavevmode

\end{center}
\end{figure}
