savoirs-vivants/station-analyse-qualite-eau/firmware/Docs/latex/test__lorawan_8c.tex

\doxysection{C:\+/\+\+Users/\+valen/\+\+Documents/\+\+BUT GEII/\+\+SAE601/\+station\+\_\+analyse\+\_\+qualite\+\_\+eau/\+firmware/\+station\+\_\+analyse\+\_\+qualite\+\_\+eau/\+\+Core/\+\+Src/\+test\+\_\+lorawan.c File Reference}
\hypertarget{test__lorawan_8c}{}\label{test__lorawan_8c}\index{C:/Users/valen/Documents/BUT GEII/SAE601/station\_analyse\_qualite\_eau/firmware/station\_analyse\_qualite\_eau/Core/Src/test\_lorawan.c@{C:/Users/valen/Documents/BUT GEII/SAE601/station\_analyse\_qualite\_eau/firmware/station\_analyse\_qualite\_eau/Core/Src/test\_lorawan.c}}

Implémentation des tests de robustesse Lo\+Ra\+WAN.  

{\ttfamily \+\#include "{}test\+\_\+lorawan.\+h"{}}\newline
{\ttfamily \+\#include $<$stdio.\+h$>$}\newline
{\ttfamily \+\#include "{}main.\+h"{}}\newline
Include dependency graph for test\+\_\+lorawan.\+c:\+
\nopagebreak
\begin{figure}[H]
\begin{center}
\leavevmode
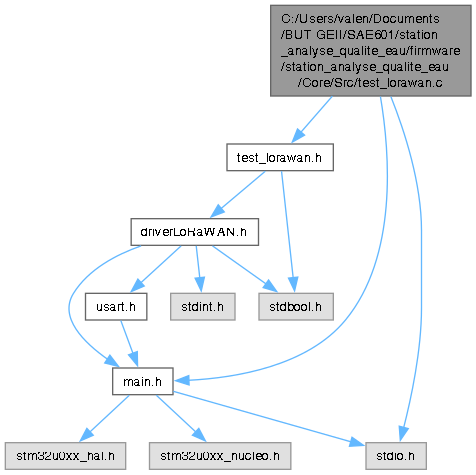
[picture p96: firmware/Docs/html/test__lorawan_8c__incl.png]

\end{center}
\end{figure}
\doxysubsubsection*{Macros}
\begin{DoxyCompactItemize}
\item 
\+\#define \doxymbox{\hyperlink{test__lorawan_8c_a2ddacbe405fe687f6fb48cdcbebf2f3b}{EXPECT}}(cond,  msg)
\item 
\+\#define \doxymbox{\hyperlink{test__lorawan_8c_a6ffea8cdf1ef4b07935b62dc59d009db}{EXPECT\+\_\+\+EQ}}(actual,  expected,  msg)
\end{DoxyCompactItemize}
\doxysubsubsection*{Functions}
\begin{DoxyCompactItemize}
\item 
bool \doxymbox{\hyperlink{test__lorawan_8c_a5b73006e7f02f8f16a186d995ae10345}{Test\+Lo\+Ra\+WAN\+\_\+\+Run\+All}} (\doxymbox{\hyperlink{struct_lo_ra_w_a_n__t}{Lo\+Ra\+WAN\+\_\+t}} \texorpdfstring{$\ast$}{*}hlora)
\begin{DoxyCompactList}\small\item\em Lance tous les tests de la couche Lo\+Ra\+WAN. \end{DoxyCompactList}\end{DoxyCompactItemize}

\doxysubsection{Detailed Description}
Implémentation des tests de robustesse Lo\+Ra\+WAN. 

\label{test__lorawan_8c_doc-define-members}
\Hypertarget{test__lorawan_8c_doc-define-members}
\doxysubsection{Macro Definition Documentation}
\Hypertarget{test__lorawan_8c_a2ddacbe405fe687f6fb48cdcbebf2f3b}\index{test\_lorawan.c@{test\_lorawan.c}!EXPECT@{EXPECT}}
\index{EXPECT@{EXPECT}!test\_lorawan.c@{test\_lorawan.c}}
\doxysubsubsection{\texorpdfstring{EXPECT}{EXPECT}}
{\footnotesize\ttfamily \label{test__lorawan_8c_a2ddacbe405fe687f6fb48cdcbebf2f3b} 
\+\#define EXPECT(\begin{DoxyParamCaption}\item[{}]{cond}{, }\item[{}]{msg}{}\end{DoxyParamCaption})}

{\bfseries Value:\+}
\begin{DoxyCode}{0}
\DoxyCodeLine{\textcolor{keywordflow}{do}\ \{\ \ \ \ \ \ \ \ \ \ \ \ \ \ \ \ \ \ \ \ \ \ \ \ \ \ \ \ \ \ \ \ \ \ \ \ \ \ \ \ \ \ \ \ \ \ \ \ \ \ \ \ \ \ \ \ \ \ \ \ \(\backslash\)}
\DoxyCodeLine{\ \ \ \ if\ (!(cond))\ \{\ \ \ \ \ \ \ \ \ \ \ \ \ \ \ \ \ \ \ \ \ \ \ \ \ \ \ \ \ \ \ \ \ \ \ \ \ \ \ \ \ \ \ \ \ \ \(\backslash\)}
\DoxyCodeLine{\ \ \ \ \ \ \ \ printf(\textcolor{stringliteral}{"{}\ \ [FAIL]\ \%s\ (ligne\ \%d)\(\backslash\)r\(\backslash\)n"{}},\ msg,\ \_\_LINE\_\_);\ \ \ \ \(\backslash\)}
\DoxyCodeLine{\ \ \ \ \ \ \ \ \textcolor{keywordflow}{return}\ \textcolor{keyword}{false};\ \ \ \ \ \ \ \ \ \ \ \ \ \ \ \ \ \ \ \ \ \ \ \ \ \ \ \ \ \ \ \ \ \ \ \ \ \ \ \ \ \ \ \(\backslash\)}
\DoxyCodeLine{\ \ \ \ \}\ \textcolor{keywordflow}{else}\ \{\ \ \ \ \ \ \ \ \ \ \ \ \ \ \ \ \ \ \ \ \ \ \ \ \ \ \ \ \ \ \ \ \ \ \ \ \ \ \ \ \ \ \ \ \ \ \ \ \ \ \ \ \(\backslash\)}
\DoxyCodeLine{\ \ \ \ \ \ \ \ printf(\textcolor{stringliteral}{"{}\ \ [\ OK\ ]\ \%s\(\backslash\)r\(\backslash\)n"{}},\ msg);\ \ \ \ \ \ \ \ \ \ \ \ \ \ \ \ \ \ \ \ \ \ \ \ \ \(\backslash\)}
\DoxyCodeLine{\ \ \ \ \}\ \ \ \ \ \ \ \ \ \ \ \ \ \ \ \ \ \ \ \ \ \ \ \ \ \ \ \ \ \ \ \ \ \ \ \ \ \ \ \ \ \ \ \ \ \ \ \ \ \ \ \ \ \ \ \ \ \ \ \(\backslash\)}
\DoxyCodeLine{\}\ \textcolor{keywordflow}{while}\ (0)}

\end{DoxyCode}
\Hypertarget{test__lorawan_8c_a6ffea8cdf1ef4b07935b62dc59d009db}\index{test\_lorawan.c@{test\_lorawan.c}!EXPECT\_EQ@{EXPECT\_EQ}}
\index{EXPECT\_EQ@{EXPECT\_EQ}!test\_lorawan.c@{test\_lorawan.c}}
\doxysubsubsection{\texorpdfstring{EXPECT\_EQ}{EXPECT\_EQ}}
{\footnotesize\ttfamily \label{test__lorawan_8c_a6ffea8cdf1ef4b07935b62dc59d009db} 
\+\#define EXPECT\+\_\+\+EQ(\begin{DoxyParamCaption}\item[{}]{actual}{, }\item[{}]{expected}{, }\item[{}]{msg}{}\end{DoxyParamCaption})}

{\bfseries Value:\+}
\begin{DoxyCode}{0}
\DoxyCodeLine{\textcolor{keywordflow}{do}\ \{\ \ \ \ \ \ \ \ \ \ \ \ \ \ \ \ \ \ \ \ \ \ \ \ \ \ \ \ \ \ \ \ \ \ \ \ \ \ \ \ \ \ \ \ \ \ \ \ \ \ \ \ \ \ \ \ \ \ \ \ \ \ \ \ \ \ \ \ \(\backslash\)}
\DoxyCodeLine{\ \ \ \ uint32\_t\ \_a\ =\ (uint32\_t)(actual);\ \ \ \ \ \ \ \ \ \ \ \ \ \ \ \ \ \ \ \ \ \ \ \ \ \ \ \ \ \ \ \ \ \ \ \(\backslash\)}
\DoxyCodeLine{\ \ \ \ uint32\_t\ \_e\ =\ (uint32\_t)(expected);\ \ \ \ \ \ \ \ \ \ \ \ \ \ \ \ \ \ \ \ \ \ \ \ \ \ \ \ \ \ \ \ \ \(\backslash\)}
\DoxyCodeLine{\ \ \ \ if\ (\_a\ !=\ \_e)\ \{\ \ \ \ \ \ \ \ \ \ \ \ \ \ \ \ \ \ \ \ \ \ \ \ \ \ \ \ \ \ \ \ \ \ \ \ \ \ \ \ \ \ \ \ \ \ \ \ \ \ \ \ \ \(\backslash\)}
\DoxyCodeLine{\ \ \ \ \ \ \ \ printf(\textcolor{stringliteral}{"{}\ \ [FAIL]\ \%s\ -\/\ Attendu:\ \%lu,\ Recu:\ \%lu\ (ligne\ \%d)\(\backslash\)r\(\backslash\)n"{}},\ \ \(\backslash\)}
\DoxyCodeLine{\ \ \ \ \ \ \ \ \ \ \ \ \ \ \ msg,\ (\textcolor{keywordtype}{unsigned}\ \textcolor{keywordtype}{long})\_e,\ (\textcolor{keywordtype}{unsigned}\ \textcolor{keywordtype}{long})\_a,\ \_\_LINE\_\_);\ \ \ \ \(\backslash\)}
\DoxyCodeLine{\ \ \ \ \ \ \ \ \textcolor{keywordflow}{return}\ \textcolor{keyword}{false};\ \ \ \ \ \ \ \ \ \ \ \ \ \ \ \ \ \ \ \ \ \ \ \ \ \ \ \ \ \ \ \ \ \ \ \ \ \ \ \ \ \ \ \ \ \ \ \ \ \ \ \(\backslash\)}
\DoxyCodeLine{\ \ \ \ \}\ \textcolor{keywordflow}{else}\ \{\ \ \ \ \ \ \ \ \ \ \ \ \ \ \ \ \ \ \ \ \ \ \ \ \ \ \ \ \ \ \ \ \ \ \ \ \ \ \ \ \ \ \ \ \ \ \ \ \ \ \ \ \ \ \ \ \ \ \ \ \(\backslash\)}
\DoxyCodeLine{\ \ \ \ \ \ \ \ printf(\textcolor{stringliteral}{"{}\ \ [\ OK\ ]\ \%s\(\backslash\)r\(\backslash\)n"{}},\ msg);\ \ \ \ \ \ \ \ \ \ \ \ \ \ \ \ \ \ \ \ \ \ \ \ \ \ \ \ \ \ \ \ \ \(\backslash\)}
\DoxyCodeLine{\ \ \ \ \}\ \ \ \ \ \ \ \ \ \ \ \ \ \ \ \ \ \ \ \ \ \ \ \ \ \ \ \ \ \ \ \ \ \ \ \ \ \ \ \ \ \ \ \ \ \ \ \ \ \ \ \ \ \ \ \ \ \ \ \ \ \ \ \ \ \ \ \(\backslash\)}
\DoxyCodeLine{\}\ \textcolor{keywordflow}{while}\ (0)}

\end{DoxyCode}

\label{test__lorawan_8c_doc-func-members}
\Hypertarget{test__lorawan_8c_doc-func-members}
\doxysubsection{Function Documentation}
\Hypertarget{test__lorawan_8c_a5b73006e7f02f8f16a186d995ae10345}\index{test\_lorawan.c@{test\_lorawan.c}!TestLoRaWAN\_RunAll@{TestLoRaWAN\_RunAll}}
\index{TestLoRaWAN\_RunAll@{TestLoRaWAN\_RunAll}!test\_lorawan.c@{test\_lorawan.c}}
\doxysubsubsection{\texorpdfstring{TestLoRaWAN\_RunAll()}{TestLoRaWAN\_RunAll()}}
{\footnotesize\ttfamily \label{test__lorawan_8c_a5b73006e7f02f8f16a186d995ae10345} 
bool Test\+Lo\+Ra\+WAN\+\_\+\+Run\+All (\begin{DoxyParamCaption}\item[{\doxymbox{\hyperlink{struct_lo_ra_w_a_n__t}{Lo\+Ra\+WAN\+\_\+t}} \texorpdfstring{$\ast$}{*}}]{hlora}{}\end{DoxyParamCaption})}

Lance tous les tests de la couche Lo\+Ra\+WAN. 

\begin{DoxyParams}{Parameters}
{\em hlora} & Pointeur vers le handle applicatif. \\
\hline
\end{DoxyParams}
\begin{DoxyReturn}{Returns}
true si tous les tests passent, false si une erreur est détectée. 
\end{DoxyReturn}
Here is the caller graph for this function:\+
\nopagebreak
\begin{figure}[H]
\begin{center}
\leavevmode

\end{center}
\end{figure}
