savoirs-vivants/station-analyse-qualite-eau/firmware/Docs/latex/test__lorawan_8h.tex

\doxysection{C:\+/\+\+Users/\+valen/\+\+Documents/\+\+BUT GEII/\+\+SAE601/\+station\+\_\+analyse\+\_\+qualite\+\_\+eau/\+firmware/\+station\+\_\+analyse\+\_\+qualite\+\_\+eau/\+\+Core/\+\+Inc/\+test\+\_\+lorawan.h File Reference}
\hypertarget{test__lorawan_8h}{}\label{test__lorawan_8h}\index{C:/Users/valen/Documents/BUT GEII/SAE601/station\_analyse\_qualite\_eau/firmware/station\_analyse\_qualite\_eau/Core/Inc/test\_lorawan.h@{C:/Users/valen/Documents/BUT GEII/SAE601/station\_analyse\_qualite\_eau/firmware/station\_analyse\_qualite\_eau/Core/Inc/test\_lorawan.h}}

Batterie de tests unitaires pour le driver Lo\+Ra\+WAN.  

{\ttfamily \+\#include "{}driver\+Lo\+Ra\+WAN.\+h"{}}\newline
{\ttfamily \+\#include $<$stdbool.\+h$>$}\newline
Include dependency graph for test\+\_\+lorawan.\+h:\+
\nopagebreak
\begin{figure}[H]
\begin{center}
\leavevmode
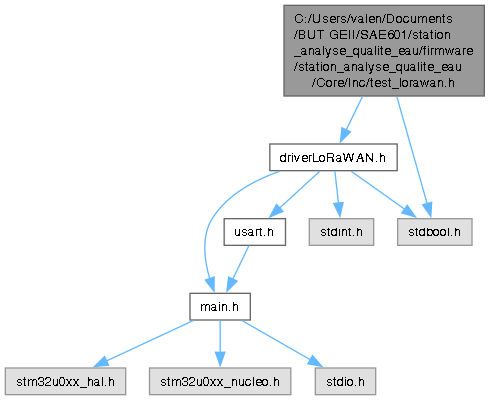
[picture p97: firmware/Docs/html/test__lorawan_8h__incl.png]

\end{center}
\end{figure}
This graph shows which files directly or indirectly include this file:\+
\nopagebreak
\begin{figure}[H]
\begin{center}
\leavevmode
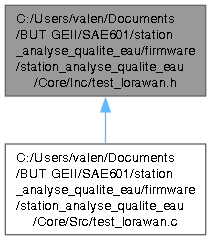
[picture p98: firmware/Docs/html/test__lorawan_8h__dep__incl.png]

\end{center}
\end{figure}
\doxysubsubsection*{Functions}
\begin{DoxyCompactItemize}
\item 
bool \doxymbox{\hyperlink{test__lorawan_8h_a5b73006e7f02f8f16a186d995ae10345}{Test\+Lo\+Ra\+WAN\+\_\+\+Run\+All}} (\doxymbox{\hyperlink{struct_lo_ra_w_a_n__t}{Lo\+Ra\+WAN\+\_\+t}} \texorpdfstring{$\ast$}{*}hlora)
\begin{DoxyCompactList}\small\item\em Lance tous les tests de la couche Lo\+Ra\+WAN. \end{DoxyCompactList}\end{DoxyCompactItemize}

\doxysubsection{Detailed Description}
Batterie de tests unitaires pour le driver Lo\+Ra\+WAN. 

\label{test__lorawan_8h_doc-func-members}
\Hypertarget{test__lorawan_8h_doc-func-members}
\doxysubsection{Function Documentation}
\Hypertarget{test__lorawan_8h_a5b73006e7f02f8f16a186d995ae10345}\index{test\_lorawan.h@{test\_lorawan.h}!TestLoRaWAN\_RunAll@{TestLoRaWAN\_RunAll}}
\index{TestLoRaWAN\_RunAll@{TestLoRaWAN\_RunAll}!test\_lorawan.h@{test\_lorawan.h}}
\doxysubsubsection{\texorpdfstring{TestLoRaWAN\_RunAll()}{TestLoRaWAN\_RunAll()}}
{\footnotesize\ttfamily \label{test__lorawan_8h_a5b73006e7f02f8f16a186d995ae10345} 
bool Test\+Lo\+Ra\+WAN\+\_\+\+Run\+All (\begin{DoxyParamCaption}\item[{\doxymbox{\hyperlink{struct_lo_ra_w_a_n__t}{Lo\+Ra\+WAN\+\_\+t}} \texorpdfstring{$\ast$}{*}}]{hlora}{}\end{DoxyParamCaption})}

Lance tous les tests de la couche Lo\+Ra\+WAN. 

\begin{DoxyParams}{Parameters}
{\em hlora} & Pointeur vers le handle applicatif. \\
\hline
\end{DoxyParams}
\begin{DoxyReturn}{Returns}
true si tous les tests passent, false si une erreur est détectée. 
\end{DoxyReturn}
Here is the caller graph for this function:\+
\nopagebreak
\begin{figure}[H]
\begin{center}
\leavevmode

\end{center}
\end{figure}
