savoirs-vivants/station-analyse-qualite-eau/firmware/Docs/latex/test__lpp_8h.tex

\doxysection{C:\+/\+\+Users/\+valen/\+\+Documents/\+\+BUT GEII/\+\+SAE601/\+station\+\_\+analyse\+\_\+qualite\+\_\+eau/\+firmware/\+station\+\_\+analyse\+\_\+qualite\+\_\+eau/\+\+Core/\+\+Inc/\+test\+\_\+lpp.h File Reference}
\hypertarget{test__lpp_8h}{}\label{test__lpp_8h}\index{C:/Users/valen/Documents/BUT GEII/SAE601/station\_analyse\_qualite\_eau/firmware/station\_analyse\_qualite\_eau/Core/Inc/test\_lpp.h@{C:/Users/valen/Documents/BUT GEII/SAE601/station\_analyse\_qualite\_eau/firmware/station\_analyse\_qualite\_eau/Core/Inc/test\_lpp.h}}

Batterie de tests unitaires pour l\textquotesingle{}encodeur Lo\+Ra\+WAN Cayenne LPP.  

{\ttfamily \+\#include "{}driver\+LPPCayenne.\+h"{}}\newline
Include dependency graph for test\+\_\+lpp.\+h:\+
\nopagebreak
\begin{figure}[H]
\begin{center}
\leavevmode
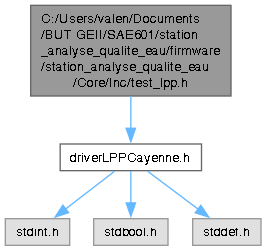
[picture p100: firmware/Docs/html/test__lpp_8h__incl.png]

\end{center}
\end{figure}
This graph shows which files directly or indirectly include this file:\+
\nopagebreak
\begin{figure}[H]
\begin{center}
\leavevmode
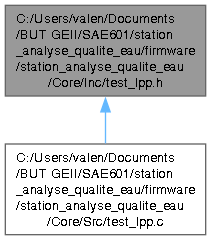
[picture p101: firmware/Docs/html/test__lpp_8h__dep__incl.png]

\end{center}
\end{figure}
\doxysubsubsection*{Functions}
\begin{DoxyCompactItemize}
\item 
bool \doxymbox{\hyperlink{test__lpp_8h_af41040cc90f3c2fdd5d5103f193751ba}{Test\+LPP\+\_\+\+Run\+All}} (void)
\begin{DoxyCompactList}\small\item\em Lance tous les tests de la couche Cayenne LPP. \end{DoxyCompactList}\end{DoxyCompactItemize}

\doxysubsection{Detailed Description}
Batterie de tests unitaires pour l\textquotesingle{}encodeur Lo\+Ra\+WAN Cayenne LPP. 

\label{test__lpp_8h_doc-func-members}
\Hypertarget{test__lpp_8h_doc-func-members}
\doxysubsection{Function Documentation}
\Hypertarget{test__lpp_8h_af41040cc90f3c2fdd5d5103f193751ba}\index{test\_lpp.h@{test\_lpp.h}!TestLPP\_RunAll@{TestLPP\_RunAll}}
\index{TestLPP\_RunAll@{TestLPP\_RunAll}!test\_lpp.h@{test\_lpp.h}}
\doxysubsubsection{\texorpdfstring{TestLPP\_RunAll()}{TestLPP\_RunAll()}}
{\footnotesize\ttfamily \label{test__lpp_8h_af41040cc90f3c2fdd5d5103f193751ba} 
bool Test\+LPP\+\_\+\+Run\+All (\begin{DoxyParamCaption}\item[{void}]{}{}\end{DoxyParamCaption})}

Lance tous les tests de la couche Cayenne LPP. 

\begin{DoxyReturn}{Returns}
true si tous les tests passent, false si une erreur est détectée. 
\end{DoxyReturn}
Here is the caller graph for this function:\+
\nopagebreak
\begin{figure}[H]
\begin{center}
\leavevmode

\end{center}
\end{figure}
