savoirs-vivants/station-analyse-qualite-eau/firmware/Docs/latex/app__main__test_8c_a4ee62d16935757fc638ff8b1b0c31188_icgraph.pdf

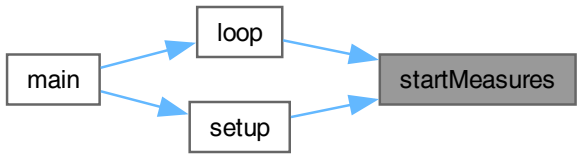
[picture p102: figure]
startMeasures; loop; setup; main
