savoirs-vivants/station-analyse-qualite-eau/firmware/Docs/latex/test__datalog_8c__incl.pdf

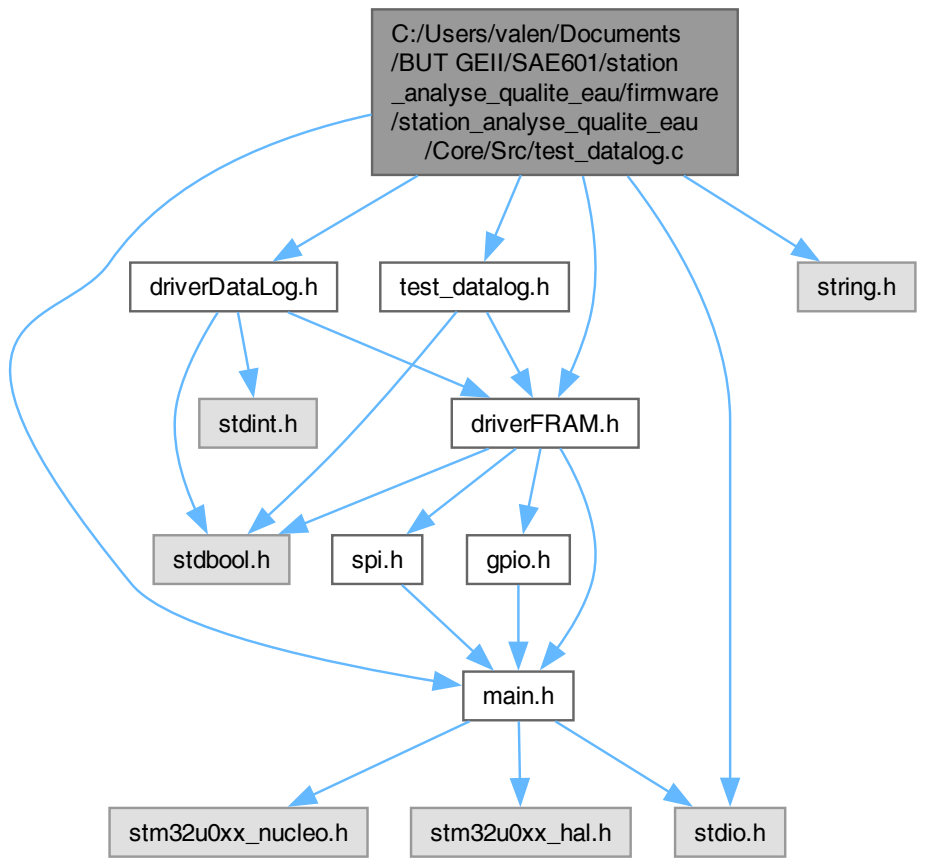
[picture p104: page 1]
test_datalog.h; driverFRAM.h; main.h; stdio.h; driverDataLog.h; string.h; stdbool.h; spi.h; gpio.h; stm32u0xx_nucleo.h; stm32u0xx_hal.h; stdint.h

C:/Users/valen/Documents
/BUT GEII/SAE601/station
_analyse_qualite_eau/firmware
/station_analyse_qualite_eau
/Core/Src/test_datalog.c
