savoirs-vivants/station-analyse-qualite-eau/firmware/station_analyse_qualite_eau/Core/Src/gpio.c

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

/* Includes ------------------------------------------------------------------*/
#include "gpio.h"

/*----------------------------------------------------------------------------*/
/* Configure GPIO                                                             */
/*----------------------------------------------------------------------------*/
/** Configure pins
     PC14-OSC32_IN   ------> RCC_OSC32_IN
     PC15-OSC32_OUT   ------> RCC_OSC32_OUT
     PF0-OSC_IN   ------> RCC_OSC_IN
     PF1-OSC_OUT   ------> RCC_OSC_OUT
     PA13 (SWDIO)   ------> DEBUG_JTMS-SWDIO
     PA14 (SWCLK)   ------> DEBUG_JTCK-SWCLK
*/
void MX_GPIO_Init(void)
{

  GPIO_InitTypeDef GPIO_InitStruct = {0};

  /* GPIO Ports Clock Enable */
  __HAL_RCC_GPIOC_CLK_ENABLE();
  __HAL_RCC_GPIOF_CLK_ENABLE();
  __HAL_RCC_GPIOA_CLK_ENABLE();
  __HAL_RCC_GPIOB_CLK_ENABLE();
  __HAL_RCC_GPIOD_CLK_ENABLE();

  /*Configure GPIO pin Output Level */
  HAL_GPIO_WritePin(GPIOA, EN_LS_C5V_Pin|EN_LS_FRAM_Pin, GPIO_PIN_RESET);

  /*Configure GPIO pin Output Level */
  HAL_GPIO_WritePin(EN_LS_LoRa_GPIO_Port, EN_LS_LoRa_Pin, GPIO_PIN_RESET);

  /*Configure GPIO pin Output Level */
  HAL_GPIO_WritePin(EN_LS_BLE_GPIO_Port, EN_LS_BLE_Pin, GPIO_PIN_RESET);

  /*Configure GPIO pin Output Level */
  HAL_GPIO_WritePin(SPI3_CS0_GPIO_Port, SPI3_CS0_Pin, GPIO_PIN_RESET);

  /*Configure GPIO pin : EN_BLE_Pin */
  GPIO_InitStruct.Pin = EN_BLE_Pin;
  GPIO_InitStruct.Mode = GPIO_MODE_IT_FALLING;
  GPIO_InitStruct.Pull = GPIO_PULLUP;
  HAL_GPIO_Init(EN_BLE_GPIO_Port, &GPIO_InitStruct);

  /*Configure GPIO pins : PF2 PF3 */
  GPIO_InitStruct.Pin = GPIO_PIN_2|GPIO_PIN_3;
  GPIO_InitStruct.Mode = GPIO_MODE_ANALOG;
  GPIO_InitStruct.Pull = GPIO_NOPULL;
  HAL_GPIO_Init(GPIOF, &GPIO_InitStruct);

  /*Configure GPIO pins : EN_LS_C5V_Pin EN_LS_FRAM_Pin */
  GPIO_InitStruct.Pin = EN_LS_C5V_Pin|EN_LS_FRAM_Pin;
  GPIO_InitStruct.Mode = GPIO_MODE_OUTPUT_PP;
  GPIO_InitStruct.Pull = GPIO_NOPULL;
  GPIO_InitStruct.Speed = GPIO_SPEED_FREQ_LOW;
  HAL_GPIO_Init(GPIOA, &GPIO_InitStruct);

  /*Configure GPIO pins : PA6 PA7 PA9 PA10
                           PA11 PA12 PA15 */
  GPIO_InitStruct.Pin = GPIO_PIN_6|GPIO_PIN_7|GPIO_PIN_9|GPIO_PIN_10
                          |GPIO_PIN_11|GPIO_PIN_12|GPIO_PIN_15;
  GPIO_InitStruct.Mode = GPIO_MODE_ANALOG;
  GPIO_InitStruct.Pull = GPIO_NOPULL;
  HAL_GPIO_Init(GPIOA, &GPIO_InitStruct);

  /*Configure GPIO pin : EN_LS_LoRa_Pin */
  GPIO_InitStruct.Pin = EN_LS_LoRa_Pin;
  GPIO_InitStruct.Mode = GPIO_MODE_OUTPUT_PP;
  GPIO_InitStruct.Pull = GPIO_NOPULL;
  GPIO_InitStruct.Speed = GPIO_SPEED_FREQ_LOW;
  HAL_GPIO_Init(EN_LS_LoRa_GPIO_Port, &GPIO_InitStruct);

  /*Configure GPIO pins : PB2 PB10 PB11 PB13
                           PB15 PB3 PB4 PB5
                           PB6 PB7 */
  GPIO_InitStruct.Pin = GPIO_PIN_2|GPIO_PIN_10|GPIO_PIN_11|GPIO_PIN_13
                          |GPIO_PIN_15|GPIO_PIN_3|GPIO_PIN_4|GPIO_PIN_5
                          |GPIO_PIN_6|GPIO_PIN_7;
  GPIO_InitStruct.Mode = GPIO_MODE_ANALOG;
  GPIO_InitStruct.Pull = GPIO_NOPULL;
  HAL_GPIO_Init(GPIOB, &GPIO_InitStruct);

  /*Configure GPIO pin : IMP_Pin */
  GPIO_InitStruct.Pin = IMP_Pin;
  GPIO_InitStruct.Mode = GPIO_MODE_INPUT;
  GPIO_InitStruct.Pull = GPIO_NOPULL;
  HAL_GPIO_Init(IMP_GPIO_Port, &GPIO_InitStruct);

  /*Configure GPIO pins : PC7 PC8 */
  GPIO_InitStruct.Pin = GPIO_PIN_7|GPIO_PIN_8;
  GPIO_InitStruct.Mode = GPIO_MODE_ANALOG;
  GPIO_InitStruct.Pull = GPIO_NOPULL;
  HAL_GPIO_Init(GPIOC, &GPIO_InitStruct);

  /*Configure GPIO pin : EN_LS_BLE_Pin */
  GPIO_InitStruct.Pin = EN_LS_BLE_Pin;
  GPIO_InitStruct.Mode = GPIO_MODE_OUTPUT_PP;
  GPIO_InitStruct.Pull = GPIO_NOPULL;
  GPIO_InitStruct.Speed = GPIO_SPEED_FREQ_LOW;
  HAL_GPIO_Init(EN_LS_BLE_GPIO_Port, &GPIO_InitStruct);

  /*Configure GPIO pin : SPI3_CS0_Pin */
  GPIO_InitStruct.Pin = SPI3_CS0_Pin;
  GPIO_InitStruct.Mode = GPIO_MODE_OUTPUT_PP;
  GPIO_InitStruct.Pull = GPIO_NOPULL;
  GPIO_InitStruct.Speed = GPIO_SPEED_FREQ_LOW;
  HAL_GPIO_Init(SPI3_CS0_GPIO_Port, &GPIO_InitStruct);

  /* EXTI interrupt init*/
  HAL_NVIC_SetPriority(EXTI4_15_IRQn, 0, 0);
  HAL_NVIC_EnableIRQ(EXTI4_15_IRQn);

}
