savoirs-vivants/station-analyse-qualite-eau/firmware/station_analyse_qualite_eau/Core/Inc/app_main_test.h

/*
 * app_main_test.h
 *
 *  Created on: 25 mars 2026
 *      Author: valen
 */

#ifndef INC_APP_MAIN_TEST_H_
#define INC_APP_MAIN_TEST_H_

#include <stdbool.h>

void setup(void);
void loop(void);

#endif /* INC_APP_MAIN_TEST_H_ */
