savoirs-vivants/station-analyse-qualite-eau/firmware/station_analyse_qualite_eau/Core/Inc/test_ds18b20.h

/*
 * test_ds18b20.h
 *
 *  Created on: 4 mai 2026
 *      Author: valen
 */

#ifndef INC_TEST_DS18B20_H_
#define INC_TEST_DS18B20_H_

#include <stdbool.h>

#include "driverDS18B20.h"

bool TestDS18B20_RunAll(DS18B20_t *hds);

#endif /* INC_TEST_DS18B20_H_ */
