savoirs-vivants/station-analyse-qualite-eau/firmware/station_analyse_qualite_eau/Core/Inc/test_lpp.h

/**
 * @file    test_lpp.h
 * @brief   Batterie de tests unitaires pour l'encodeur LoRaWAN Cayenne LPP.
 */

#ifndef INC_TEST_LPP_H_
#define INC_TEST_LPP_H_

#include "driverLPPCayenne.h"

/**
 * @brief  Lance tous les tests de la couche Cayenne LPP.
 * @return true si tous les tests passent, false si une erreur est détectée.
 */
bool TestLPP_RunAll(void);

#endif /* INC_TEST_LPP_H_ */
